PubInv/EcoPot/hypo-Round_vs_Flat/Screenshot 2025-10-10 at 23.31.12.png

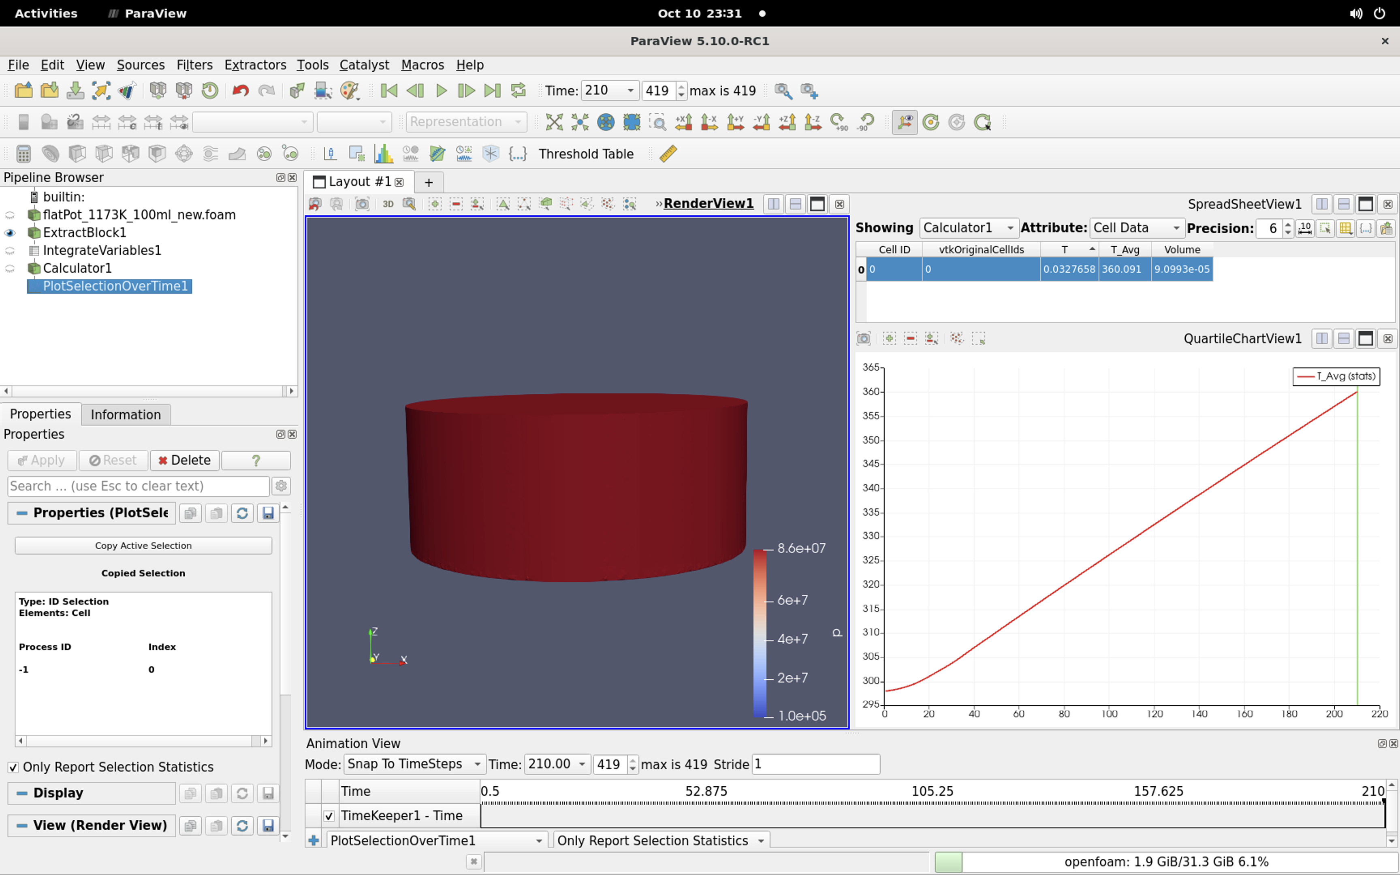
hypo-Round_vs_Flat/Screenshot 2025-10-10 at 23.31.12.png
