PubInv/EcoPot/hypo-Round_vs_Flat/Screenshot 2025-10-10 at 23.35.48.png

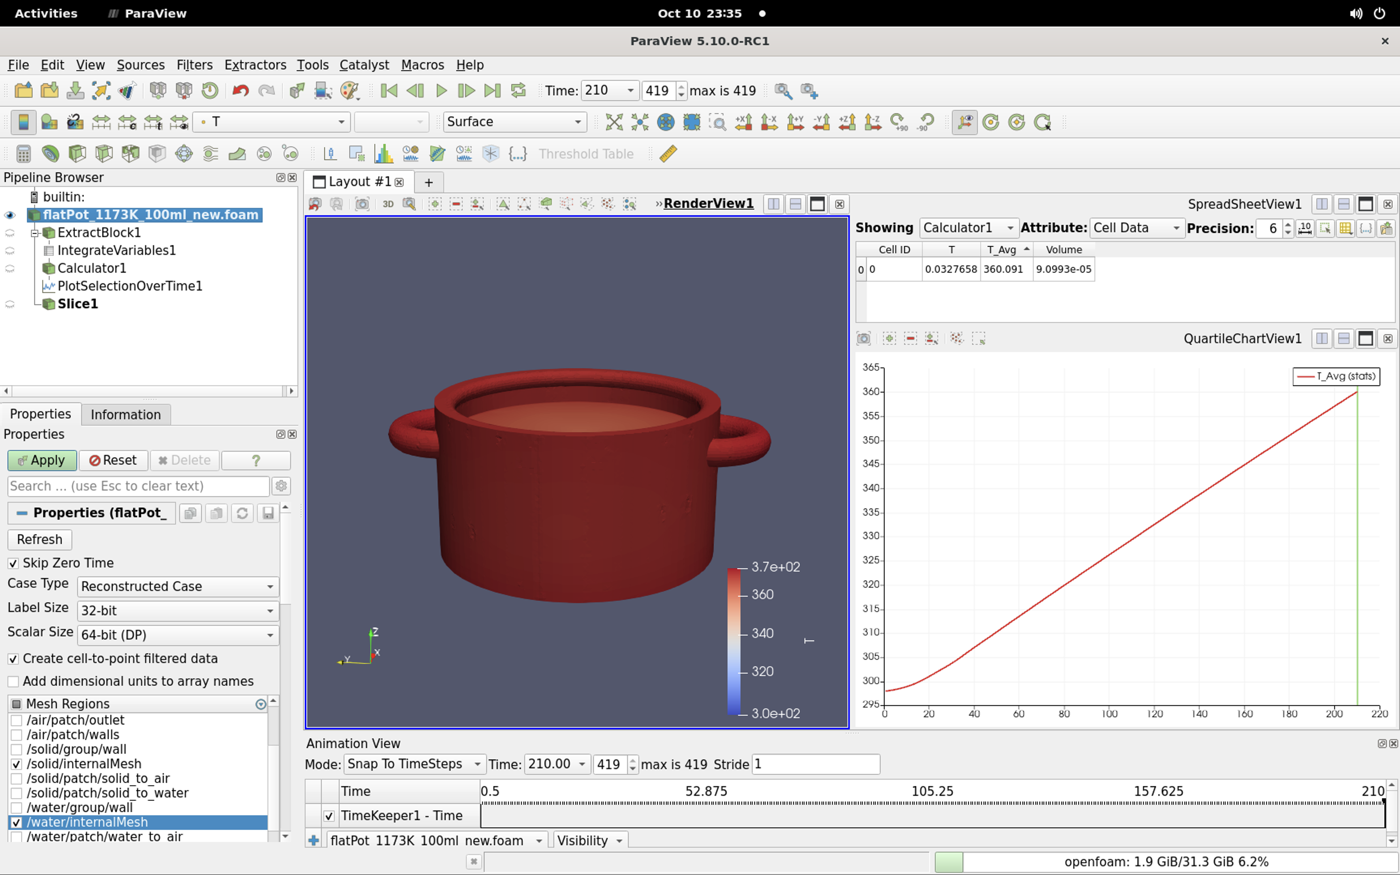
hypo-Round_vs_Flat/Screenshot 2025-10-10 at 23.35.48.png
