PubInv/EcoPot/OpenFOAM/rectangularPot_case/constant/geometry/rectangularPot.stl

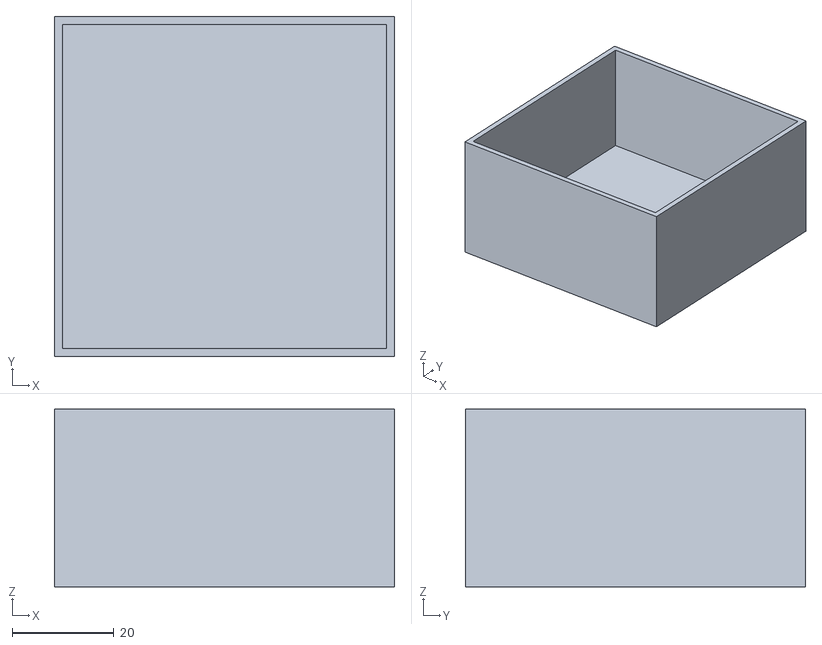
[picture p47: CAD file, 2025-06-29]
OpenFOAM/rectangularPot_case/constant/geometry/rectangularPot.stl
67.0 x 67.0 x 35.1
