PubInv/EcoPot/OpenFOAM/rectangularPot_case/templates/constant/geometry/rectangularPotContent.stl

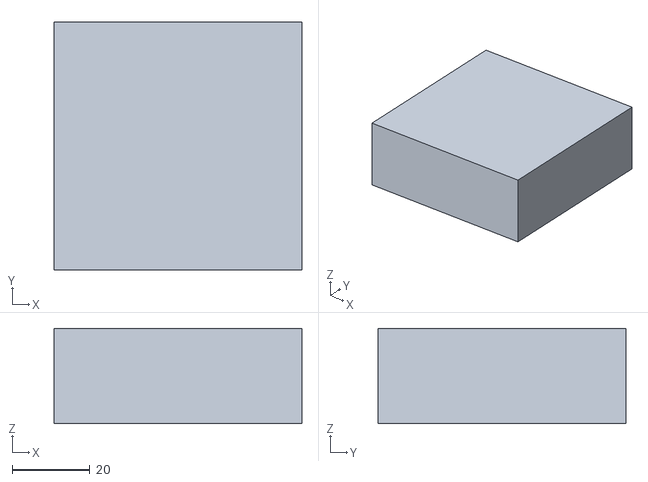
[picture p48: CAD file, 2025-06-29]
OpenFOAM/rectangularPot_case/templates/constant/geometry/rectangularPotContent.stl
63.8 x 63.8 x 24.5
