PubInv/EcoPot/OpenFOAM/roundPot_873K_100ml_36thickFins/constant/geometry/pot_roundfins.stl

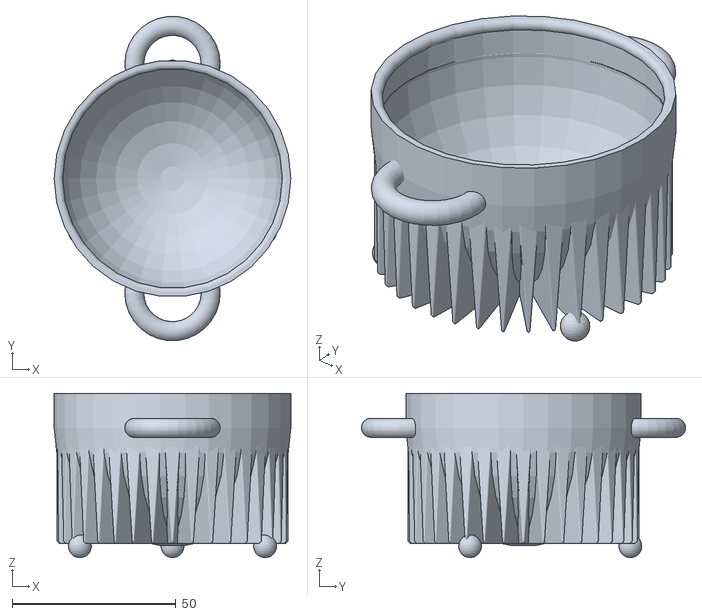
[picture p49: CAD file, 2025-12-26]
OpenFOAM/roundPot_873K_100ml_36thickFins/constant/geometry/pot_roundfins.stl
72.3 x 99.0 x 50.1
