PubInv/EcoPot/OpenFOAM/snappyMultiRegionHeater/constant/triSurface/geom.stl

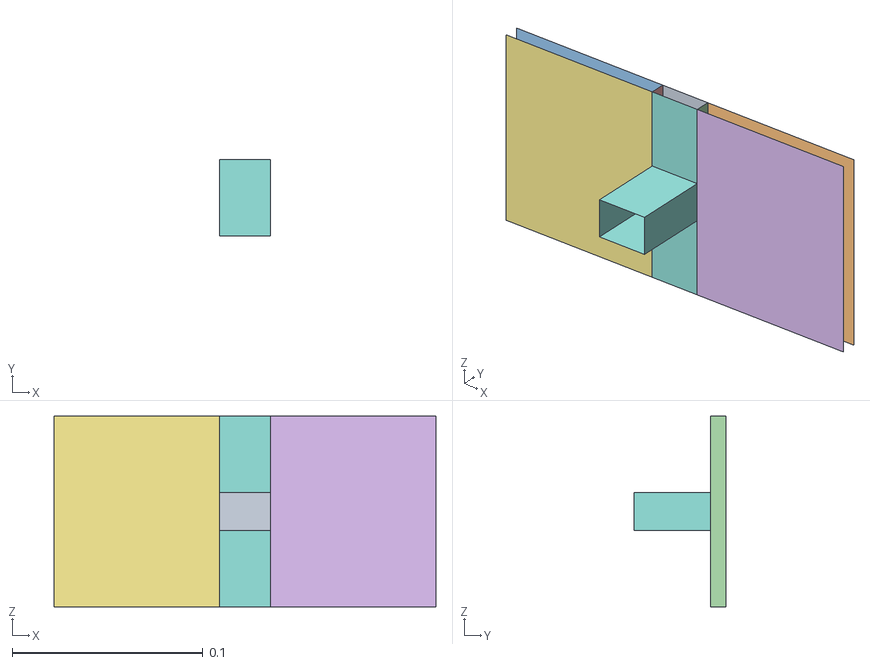
[picture p50: CAD file, 2024-10-04]
OpenFOAM/snappyMultiRegionHeater/constant/triSurface/geom.stl
0.2 x 0.048 x 0.1
topAir_to_heater
leftSolid_to_topAir
rightSolid_to_topAir
leftSolid_to_heater
rightSolid_to_heater
leftSolid_to_bottomAir
rightSolid_to_bottomAir
heater_to_bottomAir
