PubInv/EcoPot/OpenFOAM/wavyPot_873K_100ml_conicalLid/constant/geometry/wavy_water_real.stl

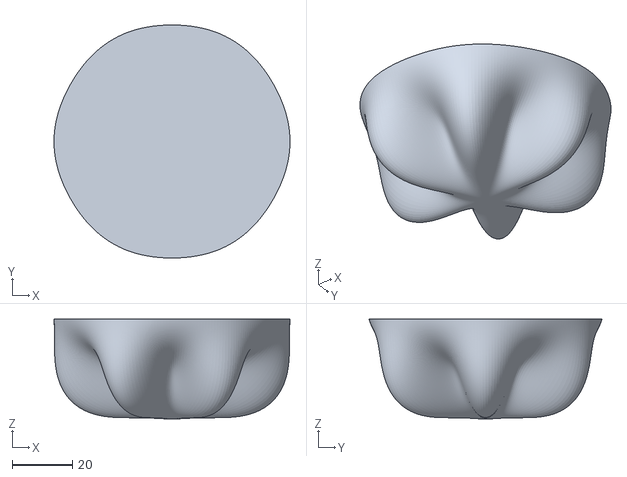
[picture p51: CAD file, 2026-08-23]
OpenFOAM/wavyPot_873K_100ml_conicalLid/constant/geometry/wavy_water_real.stl
78.1 x 77.2 x 33.1
