PubInv/EcoPot/pot-designs/2 Inch Pots used for Shapeways ECOPOT/Standard Pot 2 Inch.SLDPRT

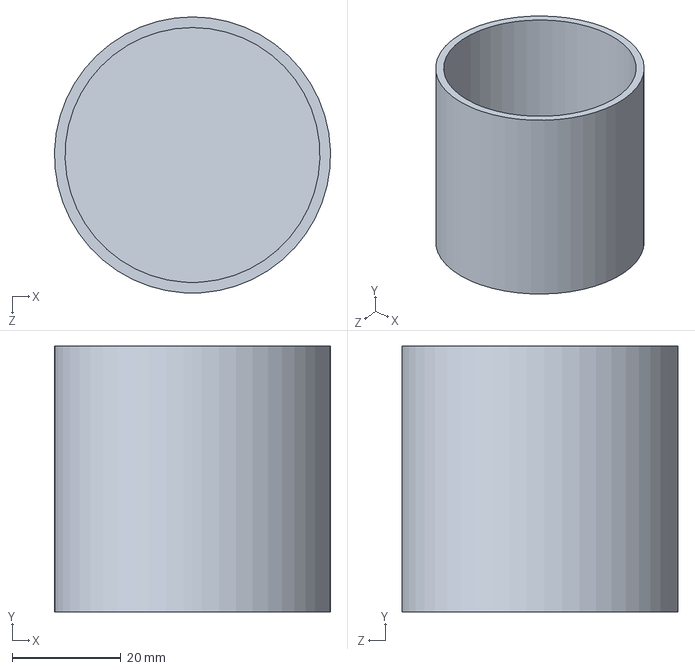
[picture p52: CAD file, 2021-05-05]
pot-designs/2 Inch Pots used for Shapeways ECOPOT/Standard Pot 2 Inch.SLDPRT
50.8 x 48.8 x 50.8 mm
