PubInv/EcoPot/pot-designs/Heat Gun Attachment FreeCAD Sketch.dxf

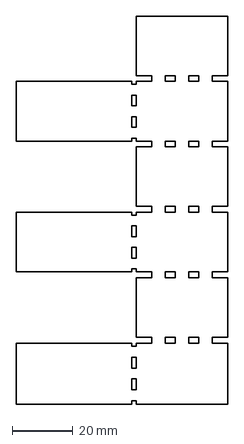
[picture p53: CAD file, 2025-12-03]
pot-designs/Heat Gun Attachment FreeCAD Sketch.dxf
69.5 x 127.7 mm
