PubInv/EcoPot/pot-STLS/TestApparatus.3mf

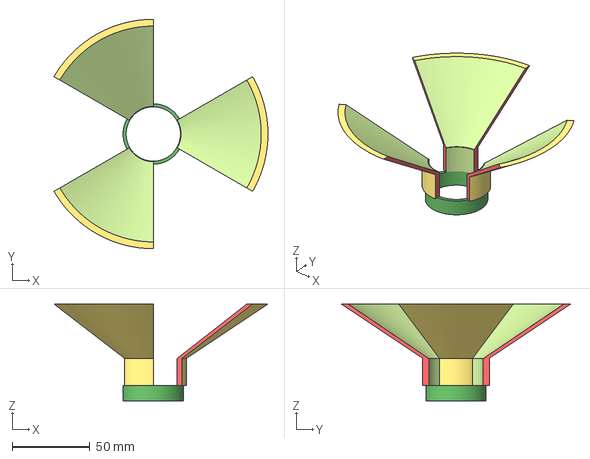
[picture p54: CAD file, 2025-10-04]
pot-STLS/TestApparatus.3mf
138.0 x 147.9 x 62.5 mm
