PubInv/EcoPot/Prototypes and Testing--Rice Team/Models _ Simulations/Generation 1 Models - Concept Ideation and Creation/Helical Vane Inner Pot v2.SLDPRT

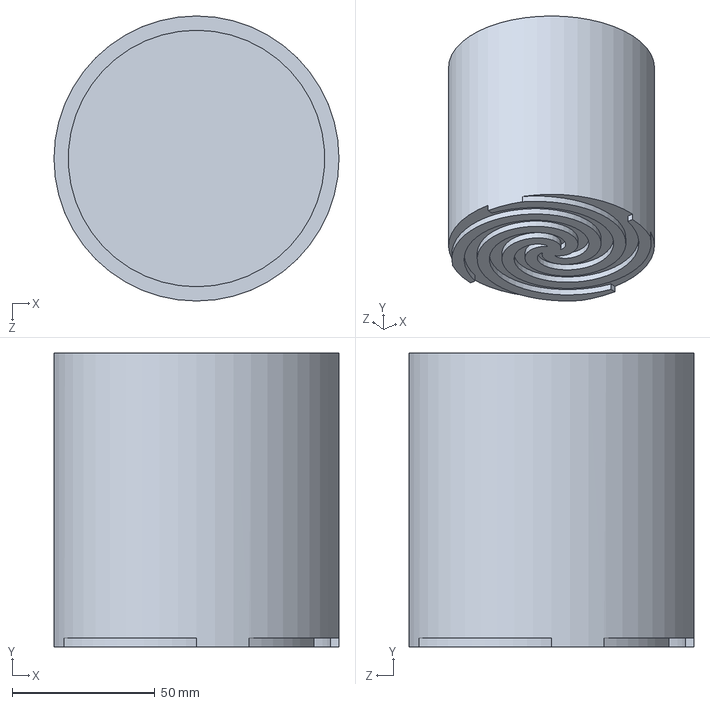
[picture p55: CAD file, 2021-06-08]
Prototypes and Testing--Rice Team/Models _ Simulations/Generation 1 Models - Concept Ideation and Creation/Helical Vane Inner Pot v2.SLDPRT
100.0 x 103.0 x 100.0 mm
