PubInv/EcoPot/Prototypes and Testing--Rice Team/Models _ Simulations/Generation 2 Models - 2 Inch Finned Shapeways Models /Horizontal Finned Pot 2 Inch.SLDPRT

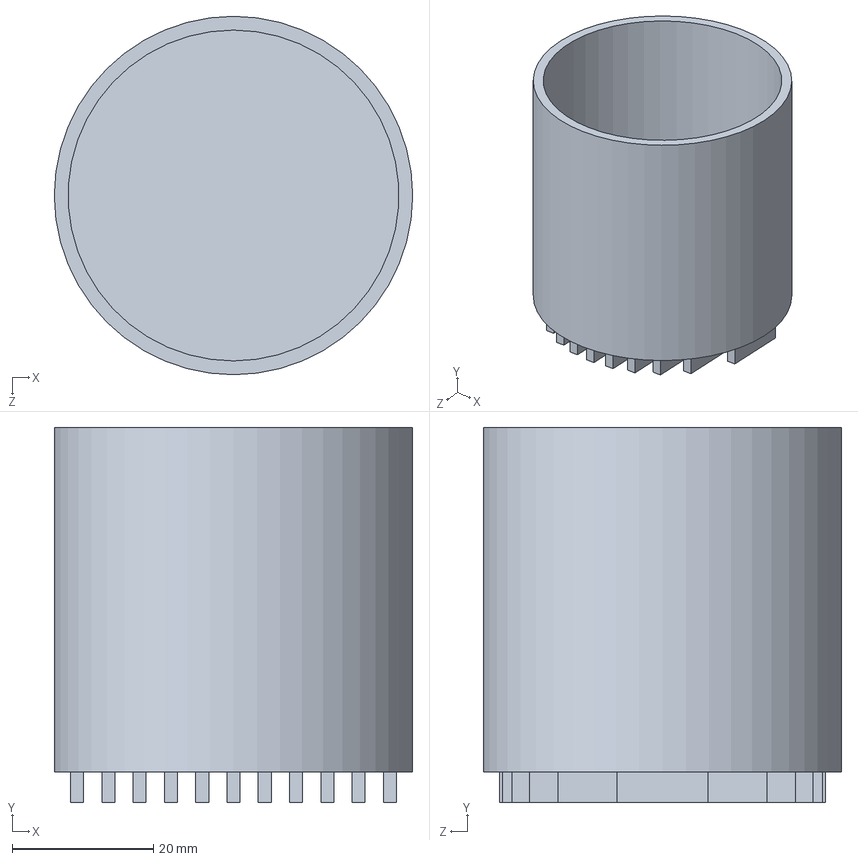
[picture p56: CAD file, 2021-06-08]
Prototypes and Testing--Rice Team/Models _ Simulations/Generation 2 Models - 2 Inch Finned Shapeways Models /Horizontal Finned Pot 2 Inch.SLDPRT
50.8 x 53.2 x 50.8 mm
