PubInv/EcoPot/Prototypes and Testing--Rice Team/Models _ Simulations/Proof of Concept Parts and STL files/Standard Pot.STL

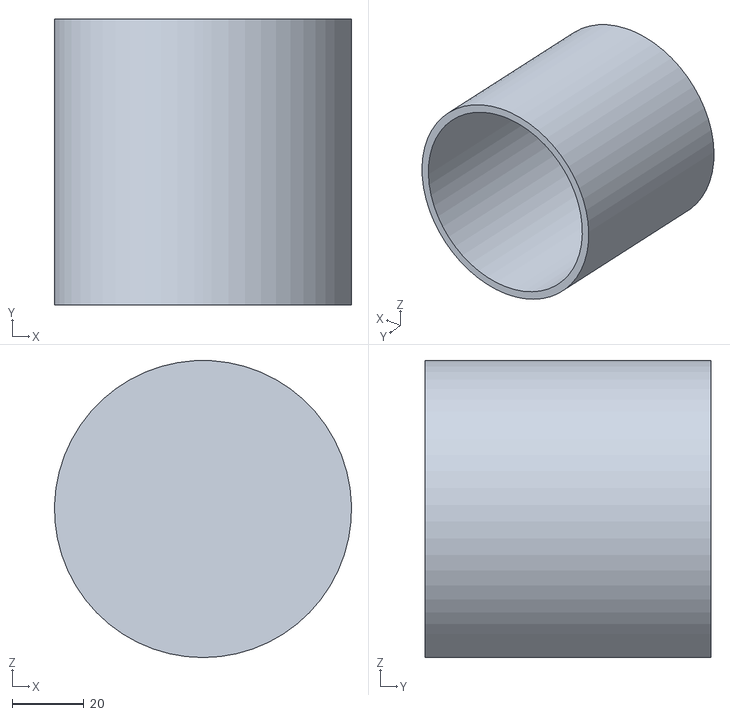
[picture p57: CAD file, 2021-06-08]
Prototypes and Testing--Rice Team/Models _ Simulations/Proof of Concept Parts and STL files/Standard Pot.STL
82.5 x 79.4 x 82.5
