PubInv/EcoPot/Prototypes and Testing--Rice Team/Models _ Simulations/Standard Pot 2 Inch Sim Setup.SLDPRT

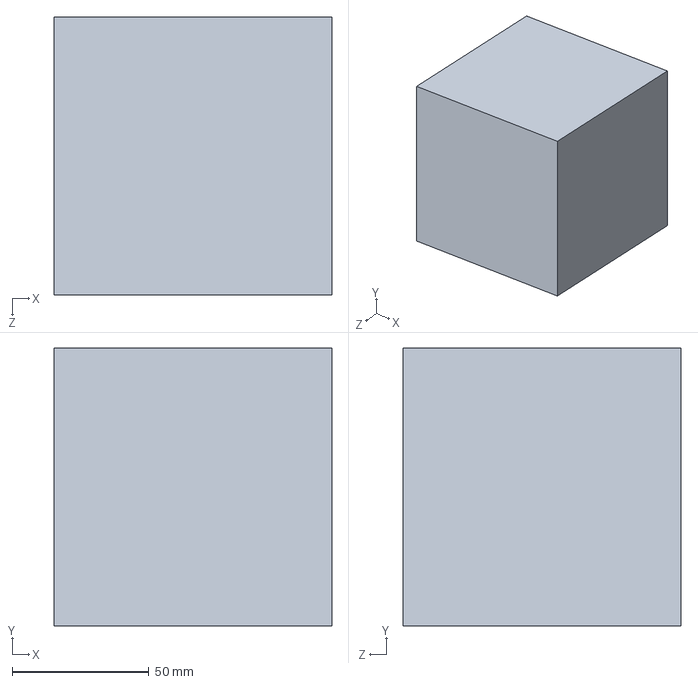
[picture p58: CAD file, 2021-06-08]
Prototypes and Testing--Rice Team/Models _ Simulations/Standard Pot 2 Inch Sim Setup.SLDPRT
101.6 x 101.6 x 101.6 mm
