PubInv/EcoPot/WavyPotSTEP/wavy_pot_vertical_meridians.step

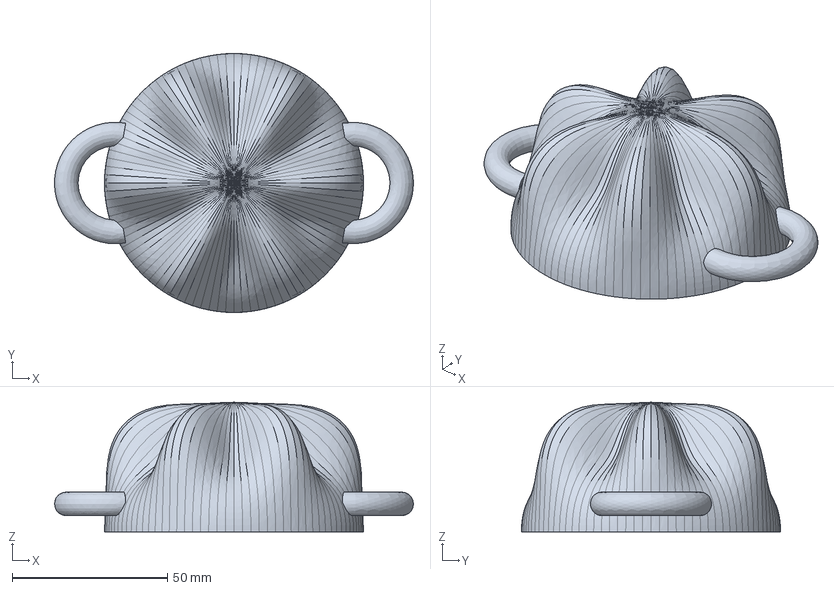
[picture p59: CAD file, 2026-05-20]
WavyPotSTEP/wavy_pot_vertical_meridians.step
115.7 x 83.5 x 41.7 mm
