PubInv/EcoPot/hypo-Round_vs_Flat/Flat_Bottom_Pot.stl

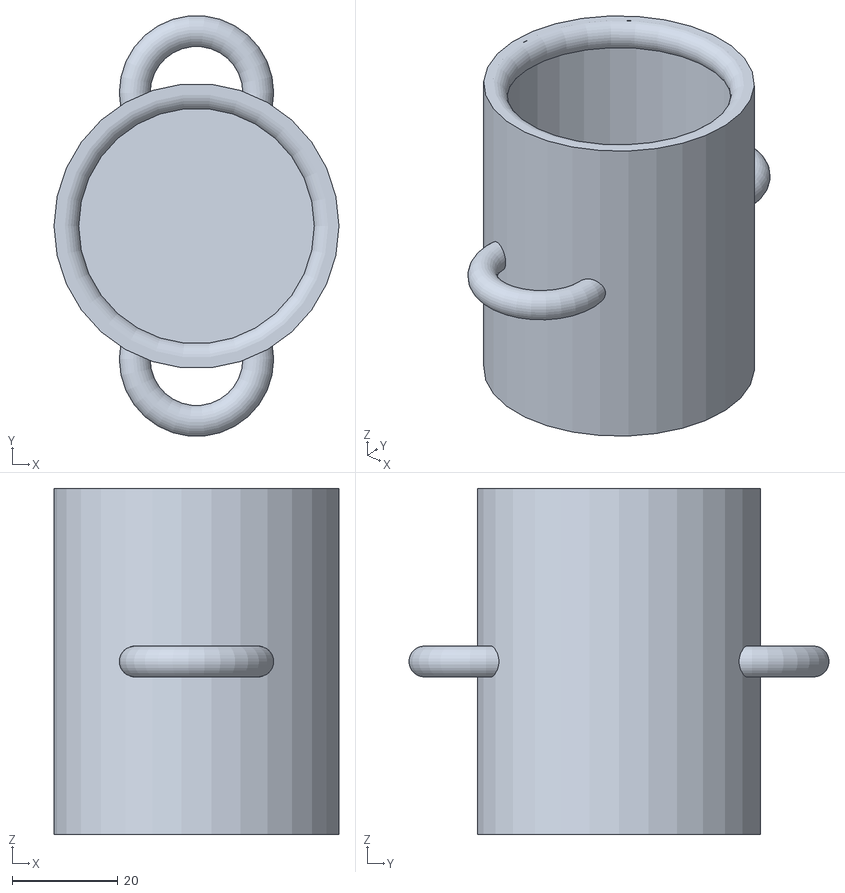
[picture p60: CAD file, 2025-07-09]
hypo-Round_vs_Flat/Flat_Bottom_Pot.stl
53.8 x 79.3 x 65.4
