PubInv/EcoPot/OpenFOAM/erlenmeyer_pot_16605mm_wall_thickness/constant/geometry/flatLid.stl

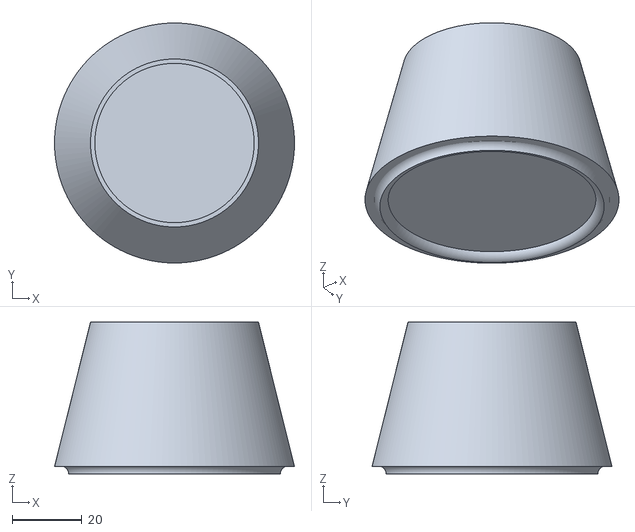
[picture p61: CAD file, 2026-04-26]
OpenFOAM/erlenmeyer_pot_16605mm_wall_thickness/constant/geometry/flatLid.stl
68.7 x 68.7 x 43.4
