PubInv/EcoPot/OpenFOAM/flatPot_1173K_100ml_widePot/constant/geometry/flatPotContentNewOne.stl

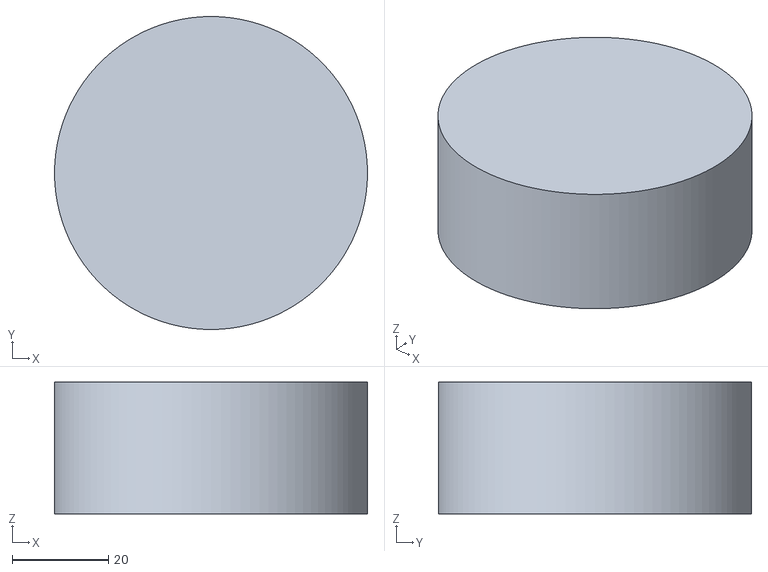
[picture p62: CAD file, 2025-10-10]
OpenFOAM/flatPot_1173K_100ml_widePot/constant/geometry/flatPotContentNewOne.stl
65.1 x 65.1 x 27.4
