PubInv/EcoPot/OpenFOAM/wavyPot_873K_100ml_conicalLid/constant/geometry/conicalLid.stl

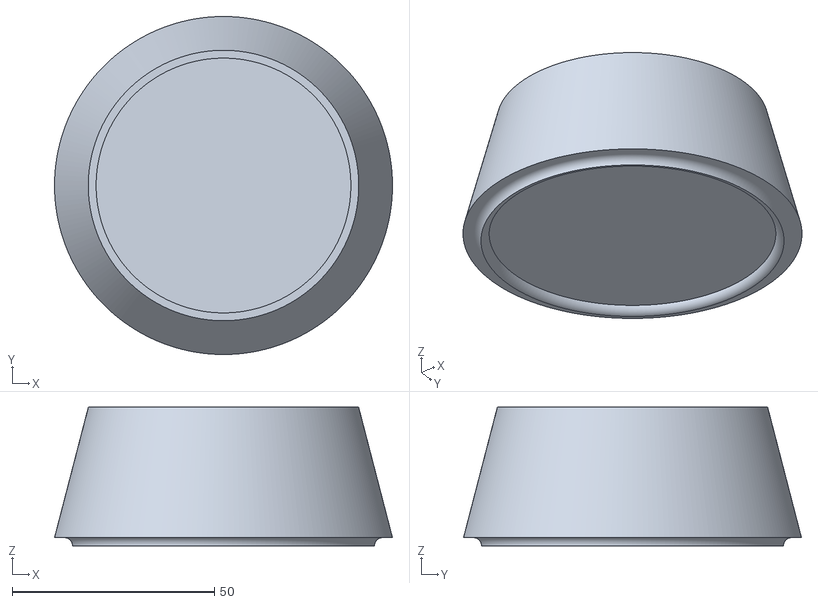
[picture p63: CAD file, 2026-08-23]
OpenFOAM/wavyPot_873K_100ml_conicalLid/constant/geometry/conicalLid.stl
83.5 x 83.5 x 34.2
