PubInv/EcoPot/pot-designs/2 Inch Pots used for Shapeways ECOPOT/Radial Half Finned Pot Rounded 2 Inch.SLDPRT

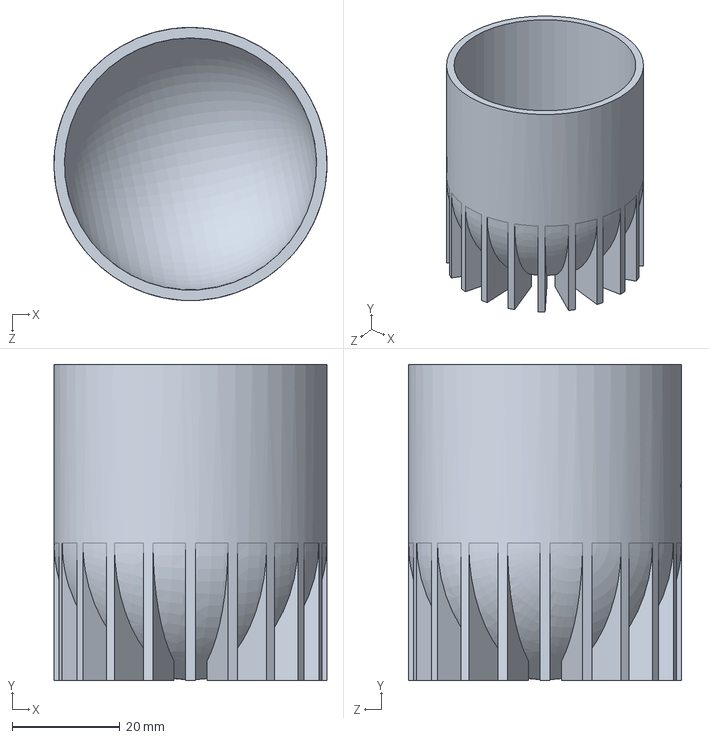
[picture p64: CAD file, 2021-05-05]
pot-designs/2 Inch Pots used for Shapeways ECOPOT/Radial Half Finned Pot Rounded 2 Inch.SLDPRT
50.8 x 58.8 x 50.8 mm
