PubInv/EcoPot/pot-designs/Heat Gun Attachment FreeCAD v1.dxf

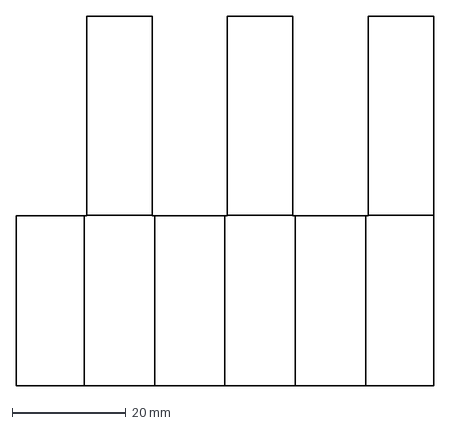
[picture p65: CAD file, 2025-11-05]
pot-designs/Heat Gun Attachment FreeCAD v1.dxf
73.5 x 65.1 mm
