PubInv/EcoPot/pot-STLS/ParameterizedPotDesigns_pot.stl

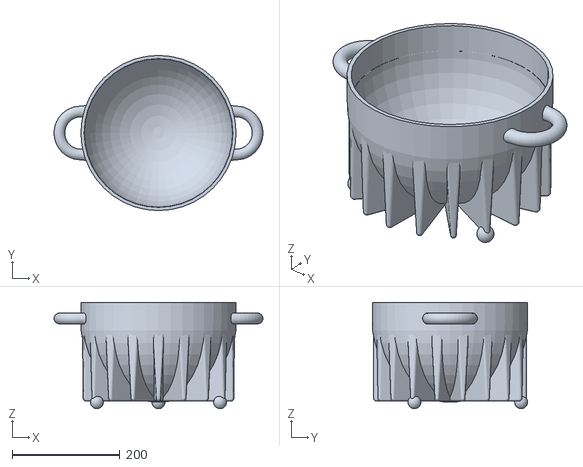
[picture p66: CAD file, 2025-02-19]
pot-STLS/ParameterizedPotDesigns_pot.stl
388.2 x 288.2 x 197.5
