PubInv/EcoPot/Prototypes and Testing--Rice Team/Models _ Simulations/Generation 1 Models - Concept Ideation and Creation/Ecopot - basic pot.SLDPRT

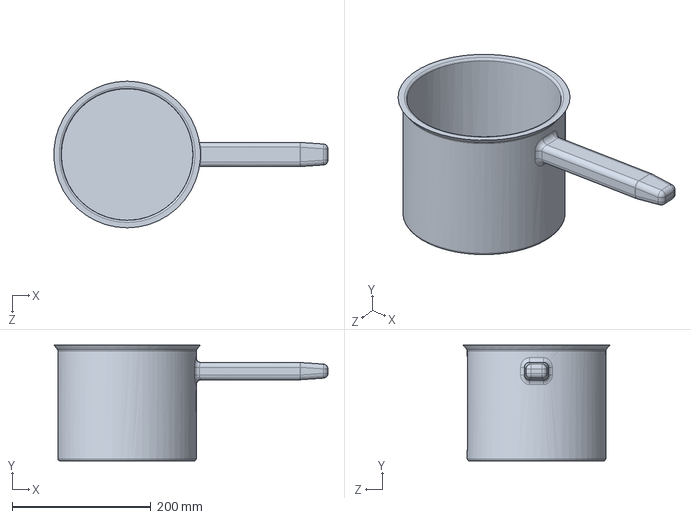
[picture p67: CAD file, 2021-06-08]
Prototypes and Testing--Rice Team/Models _ Simulations/Generation 1 Models - Concept Ideation and Creation/Ecopot - basic pot.SLDPRT
395.6 x 167.0 x 211.7 mm
