PubInv/EcoPot/Prototypes and Testing--Rice Team/Models _ Simulations/Generation 3 Models - Half Radial Fin Iterations + Fin Guard Models/Radial Half Finned Pot_40 Fins.SLDPRT

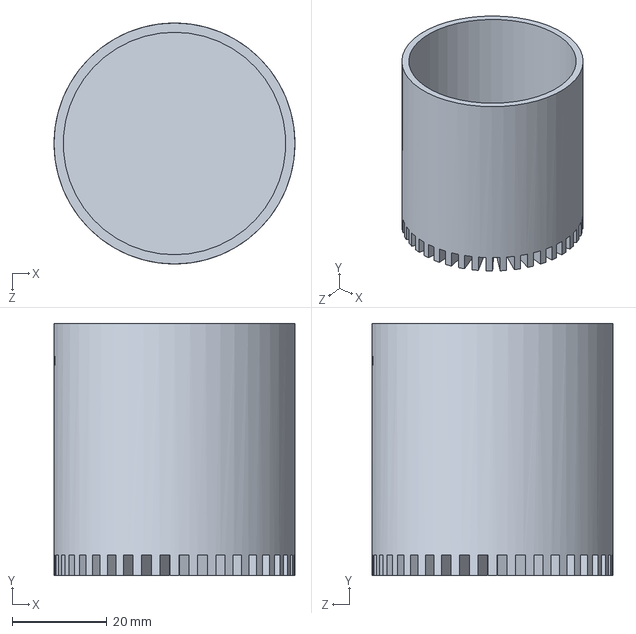
[picture p68: CAD file, 2021-06-08]
Prototypes and Testing--Rice Team/Models _ Simulations/Generation 3 Models - Half Radial Fin Iterations + Fin Guard Models/Radial Half Finned Pot_40 Fins.SLDPRT
50.8 x 53.2 x 50.8 mm
