PubInv/EcoPot/Prototypes and Testing--Rice Team/Models _ Simulations/Proof of Concept Parts and STL files/Helical Vane Outer Pot.STL

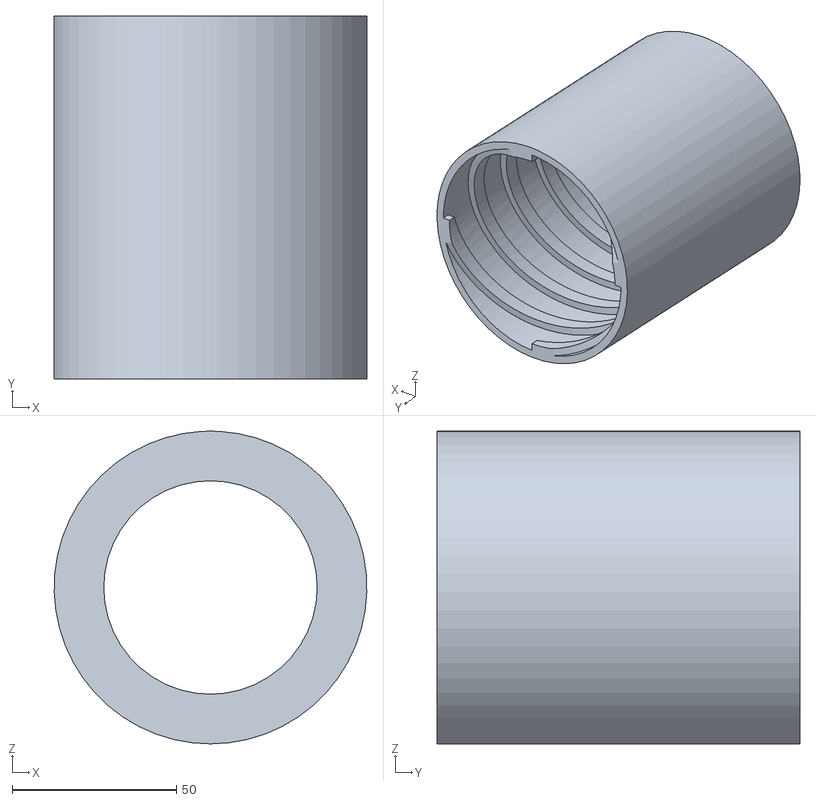
[picture p69: CAD file, 2021-06-08]
Prototypes and Testing--Rice Team/Models _ Simulations/Proof of Concept Parts and STL files/Helical Vane Outer Pot.STL
95.2 x 110.6 x 95.2
