PubInv/EcoPot/hypo-Round_vs_Flat/Rounded_Bottom_Pot.stl

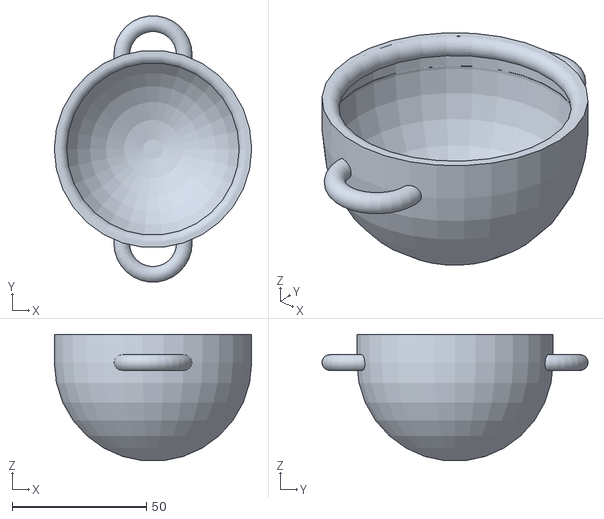
[picture p70: CAD file, 2025-07-09]
hypo-Round_vs_Flat/Rounded_Bottom_Pot.stl
73.5 x 99.0 x 47.0
