PubInv/EcoPot/OpenFOAM/erlenmeyer_pot_16605mm_wall_thickness/constant/geometry/erlenmeyerPotContent.stl

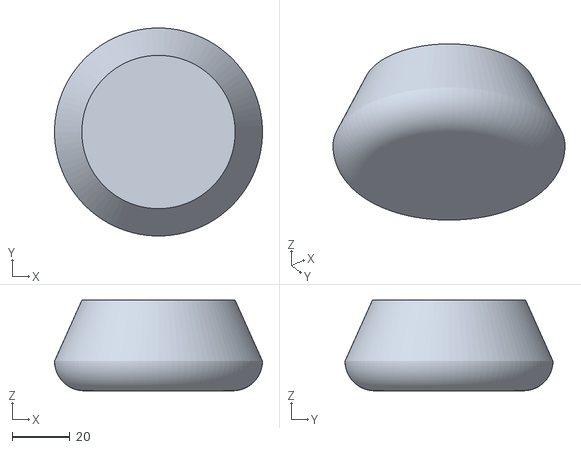
[picture p71: CAD file, 2026-04-26]
OpenFOAM/erlenmeyer_pot_16605mm_wall_thickness/constant/geometry/erlenmeyerPotContent.stl
72.0 x 72.0 x 31.4
