PubInv/EcoPot/OpenFOAM/flatPot_1173K_100ml_widePot/constant/geometry/flatPotContentNew.stl

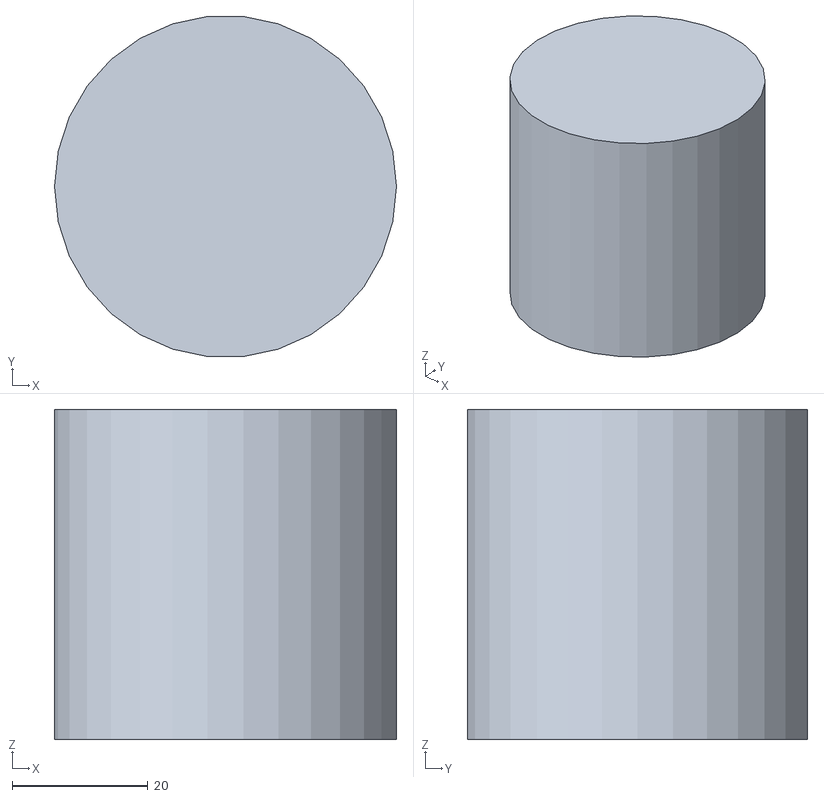
[picture p72: CAD file, 2025-07-09]
OpenFOAM/flatPot_1173K_100ml_widePot/constant/geometry/flatPotContentNew.stl
50.3 x 50.0 x 48.6
