PubInv/EcoPot/pot-designs/2 Inch Pots used for Shapeways ECOPOT/Radial Pot Rounded 2 Inch.SLDPRT

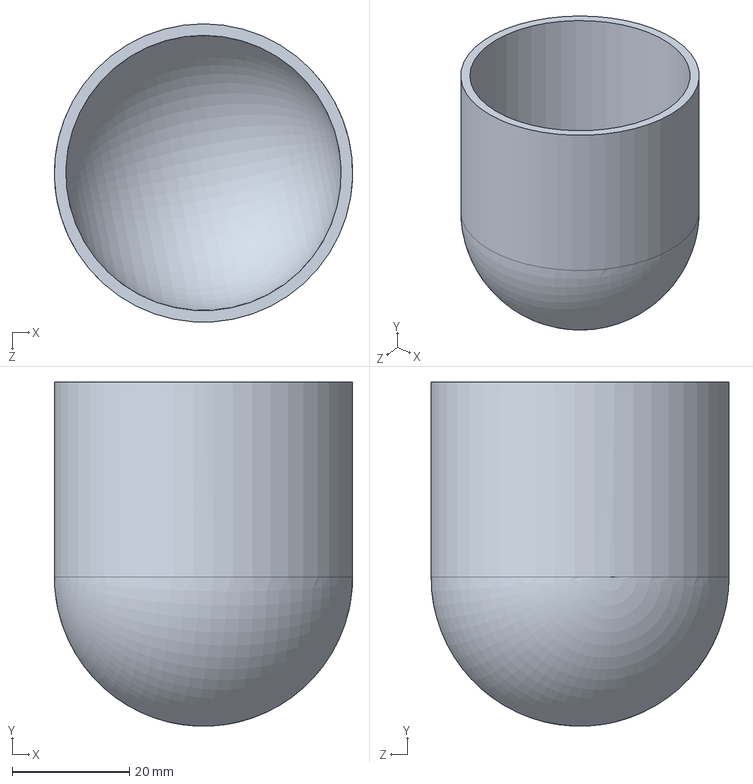
[picture p73: CAD file, 2021-05-05]
pot-designs/2 Inch Pots used for Shapeways ECOPOT/Radial Pot Rounded 2 Inch.SLDPRT
50.8 x 58.6 x 50.8 mm
