PubInv/EcoPot/pot-STLS/Crucible.stl

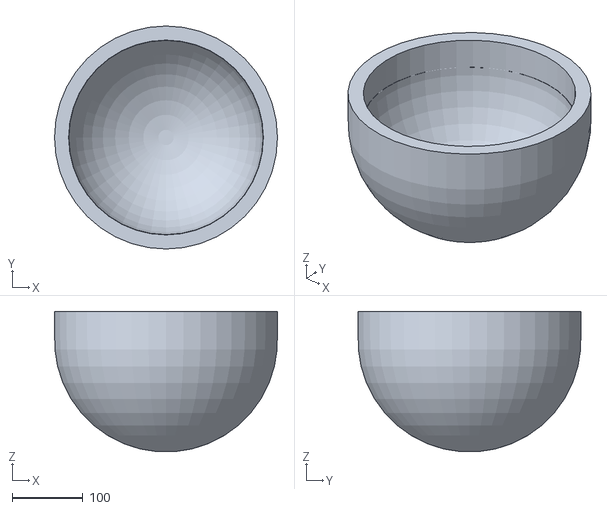
[picture p74: CAD file, 2024-09-18]
pot-STLS/Crucible.stl
316.2 x 316.2 x 199.1
