PubInv/EcoPot/Prototypes and Testing--Rice Team/Models _ Simulations/Generation 1 Models - Concept Ideation and Creation/Helical Vane Outer Pot.SLDPRT

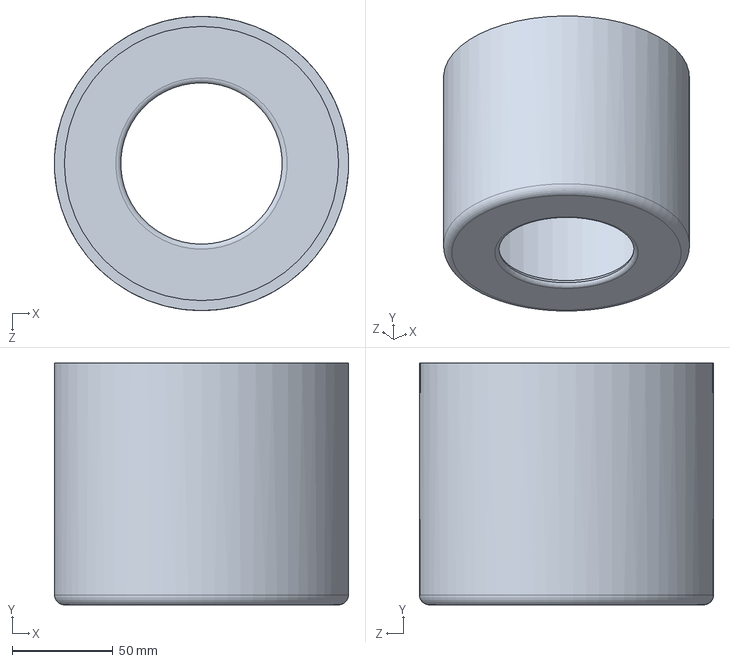
[picture p75: CAD file, 2021-06-08]
Prototypes and Testing--Rice Team/Models _ Simulations/Generation 1 Models - Concept Ideation and Creation/Helical Vane Outer Pot.SLDPRT
145.9 x 120.0 x 146.0 mm
