PubInv/EcoPot/Prototypes and Testing--Rice Team/Models _ Simulations/Generation 2 Models - 2 Inch Finned Shapeways Models /Horizontal Finned Pot.SLDPRT

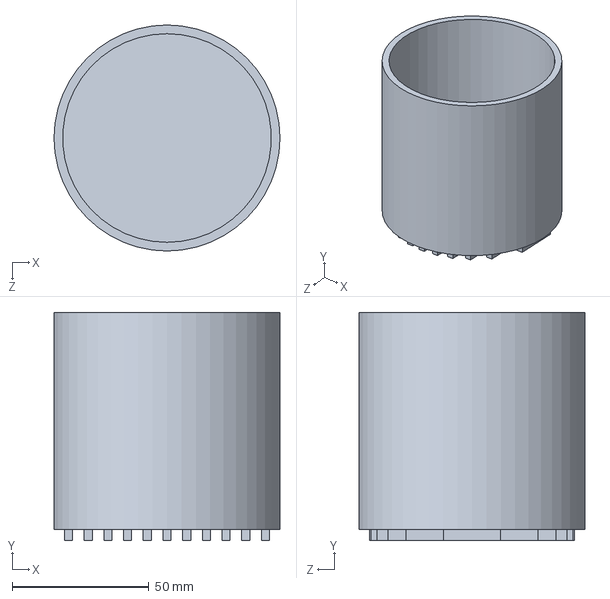
[picture p76: CAD file, 2021-06-08]
Prototypes and Testing--Rice Team/Models _ Simulations/Generation 2 Models - 2 Inch Finned Shapeways Models /Horizontal Finned Pot.SLDPRT
82.5 x 83.4 x 82.5 mm
