PubInv/EcoPot/Prototypes and Testing--Rice Team/Models _ Simulations/Proof of Concept Parts and STL files/Helical Vane Inner Pot.SLDPRT

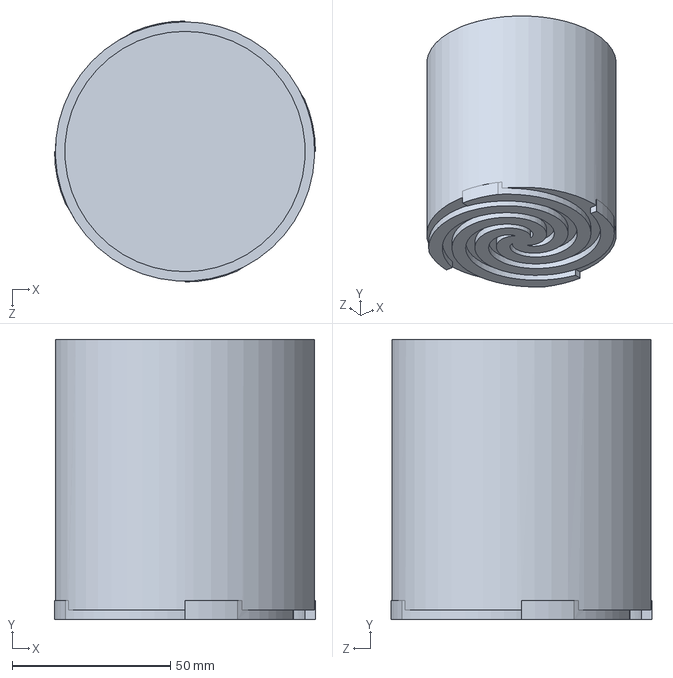
[picture p77: CAD file, 2021-06-08]
Prototypes and Testing--Rice Team/Models _ Simulations/Proof of Concept Parts and STL files/Helical Vane Inner Pot.SLDPRT
82.5 x 88.5 x 82.5 mm
