PubInv/EcoPot/OpenFOAM/erlenmeyer_pot_16605mm_wall_thickness/constant/geometry/flatPot.stl

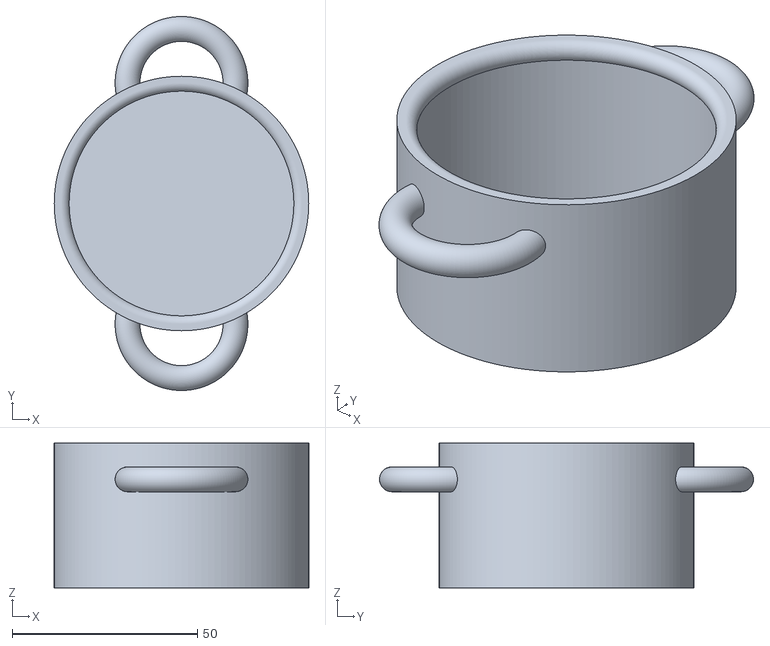
[picture p78: CAD file, 2026-04-26]
OpenFOAM/erlenmeyer_pot_16605mm_wall_thickness/constant/geometry/flatPot.stl
68.7 x 100.9 x 39.1
