PubInv/EcoPot/OpenFOAM/wavyPot_873K_100ml_conicalLid/constant/geometry/air_fire.stl

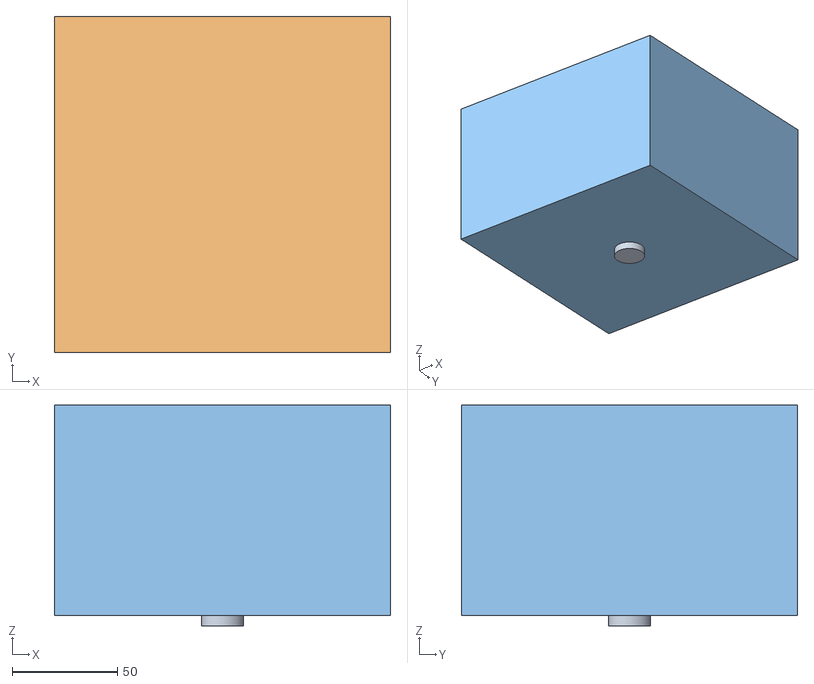
[picture p79: CAD file, 2026-08-23]
OpenFOAM/wavyPot_873K_100ml_conicalLid/constant/geometry/air_fire.stl
160.0 x 160.0 x 105.0
inlet
outlet
walls
