PubInv/EcoPot/Prototypes and Testing--Rice Team/Models _ Simulations/Generation 1 Models - Concept Ideation and Creation/Adjustable Pot Skirt.SLDPRT

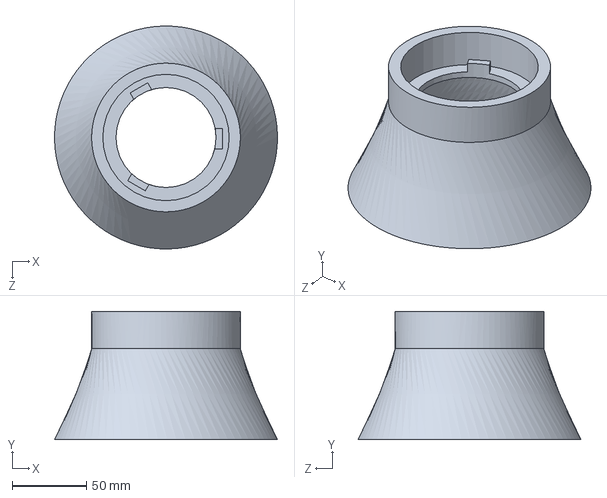
[picture p80: CAD file, 2021-06-08]
Prototypes and Testing--Rice Team/Models _ Simulations/Generation 1 Models - Concept Ideation and Creation/Adjustable Pot Skirt.SLDPRT
150.0 x 86.4 x 150.0 mm
