PubInv/EcoPot/Prototypes and Testing--Rice Team/Models _ Simulations/Generation 3 Models - Half Radial Fin Iterations + Fin Guard Models/Fin Guard Wireframe.SLDPRT

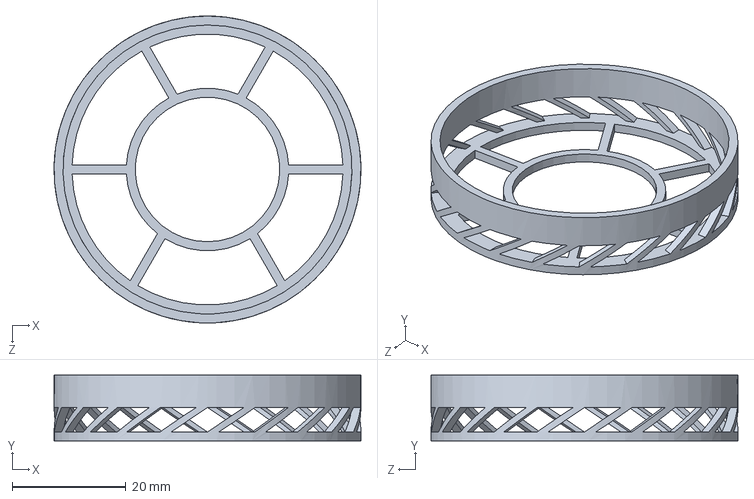
[picture p81: CAD file, 2021-06-08]
Prototypes and Testing--Rice Team/Models _ Simulations/Generation 3 Models - Half Radial Fin Iterations + Fin Guard Models/Fin Guard Wireframe.SLDPRT
54.0 x 11.6 x 54.0 mm
