PubInv/EcoPot/OpenFOAM/erlenmeyer_pot_16605mm_wall_thickness/constant/geometry/air.stl

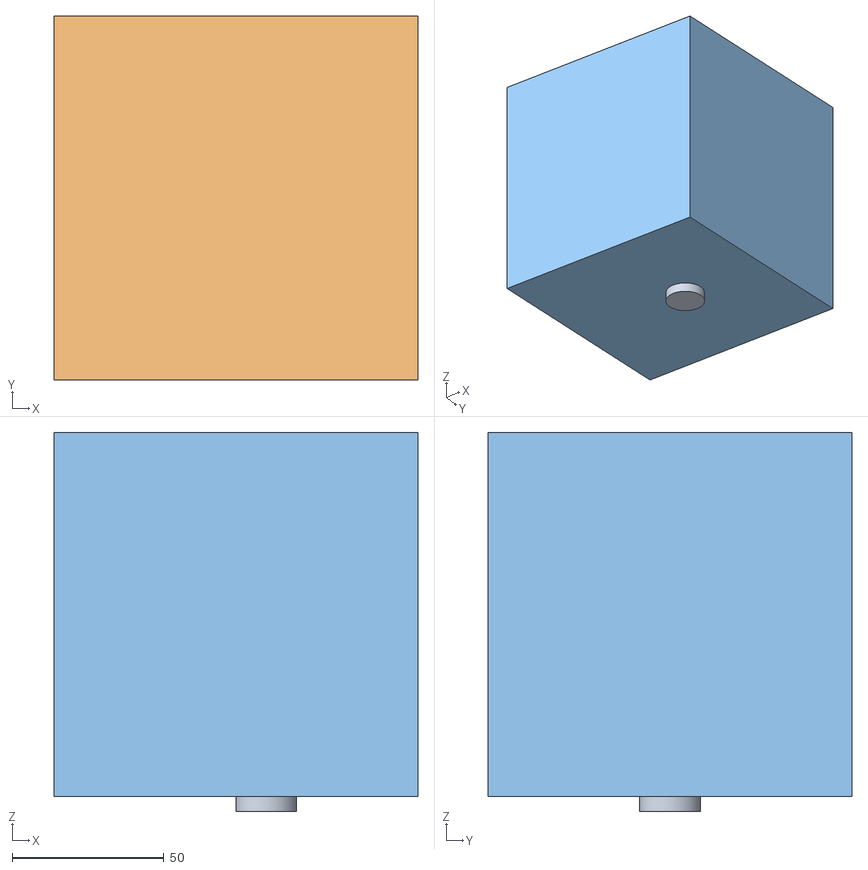
[picture p82: CAD file, 2026-04-26]
OpenFOAM/erlenmeyer_pot_16605mm_wall_thickness/constant/geometry/air.stl
120.0 x 120.0 x 125.0
inlet
outlet
walls
