PubInv/EcoPot/OpenFOAM/flatPot_1173K_100ml_widePot/constant/geometry/flatPot_mm.stl

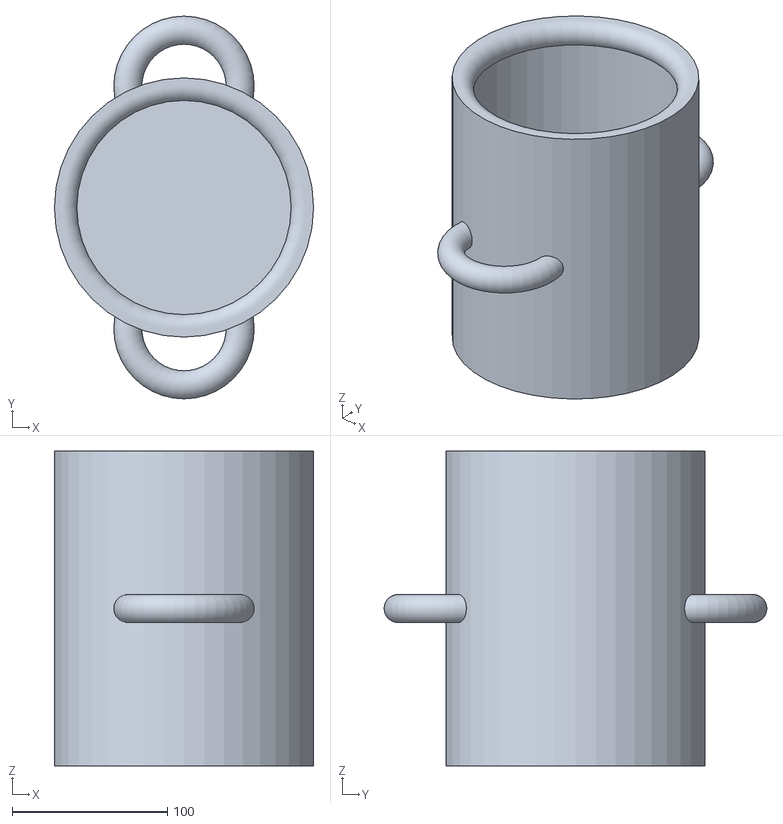
[picture p83: CAD file, 2025-06-07]
OpenFOAM/flatPot_1173K_100ml_widePot/constant/geometry/flatPot_mm.stl
167.2 x 246.9 x 203.2
