PubInv/EcoPot/OpenFOAM/wavyPot_873K_100ml_conicalLid/constant/geometry/headspace.stl

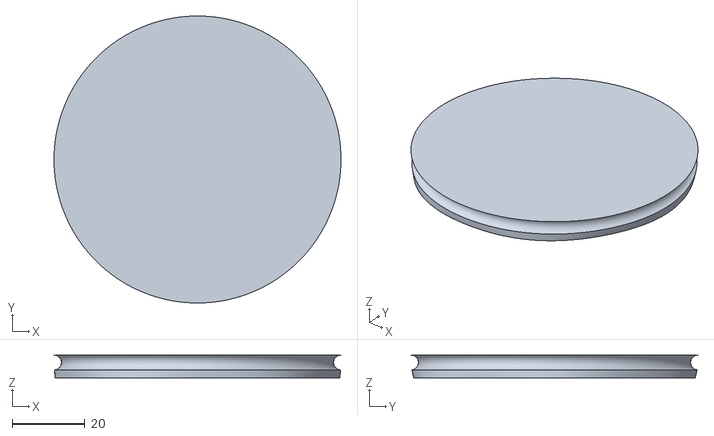
[picture p84: CAD file, 2026-08-23]
OpenFOAM/wavyPot_873K_100ml_conicalLid/constant/geometry/headspace.stl
78.7 x 78.7 x 6.23
