PubInv/EcoPot/OpenFOAM/erlenmeyer_pot_16605mm_wall_thickness/constant/geometry/erlenmeyerPot.stl

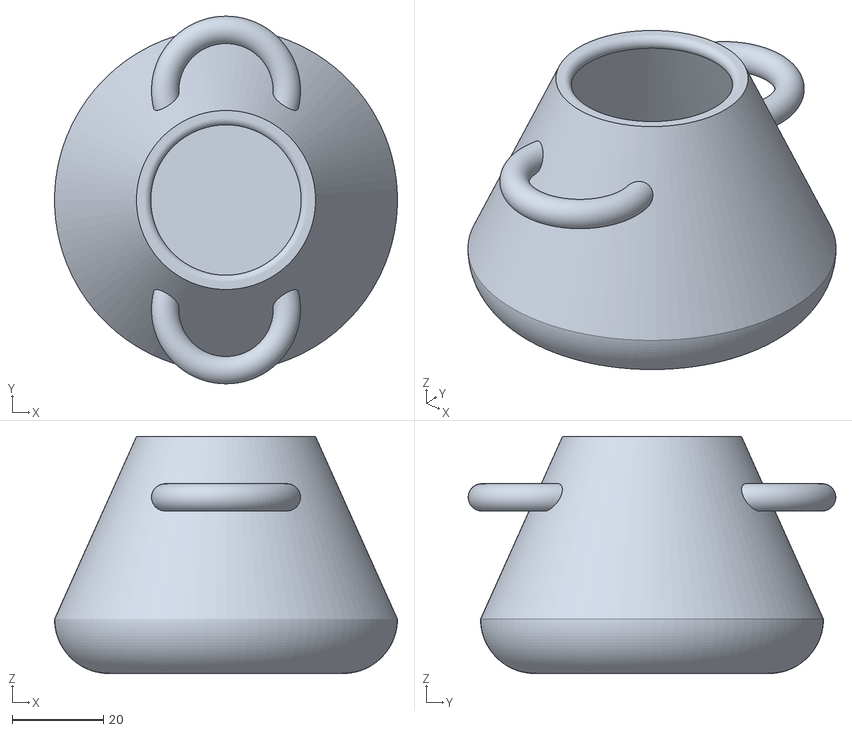
[picture p85: CAD file, 2026-04-26]
OpenFOAM/erlenmeyer_pot_16605mm_wall_thickness/constant/geometry/erlenmeyerPot.stl
75.3 x 80.7 x 52.1
