PubInv/EcoPot/OpenFOAM/wavyPot_873K_100ml_conicalLid/constant/geometry/pot200.stl

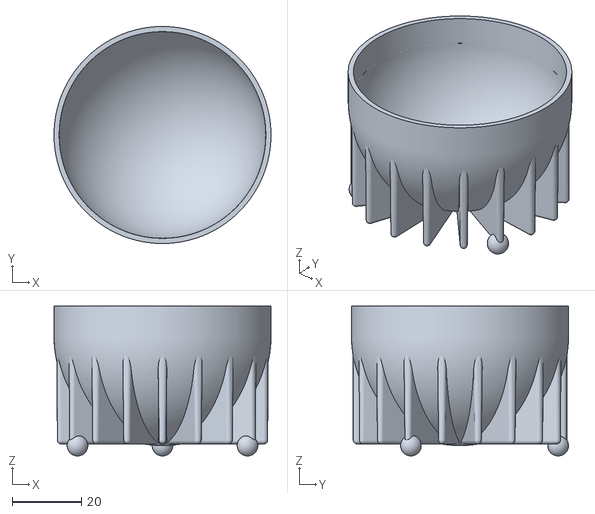
[picture p86: CAD file, 2026-04-26]
OpenFOAM/wavyPot_873K_100ml_conicalLid/constant/geometry/pot200.stl
62.5 x 62.5 x 43.1
