PubInv/EcoPot/Prototypes and Testing--Rice Team/Models _ Simulations/Generation 1 Models - Concept Ideation and Creation/FINNED HEATING PLATE.SLDPRT

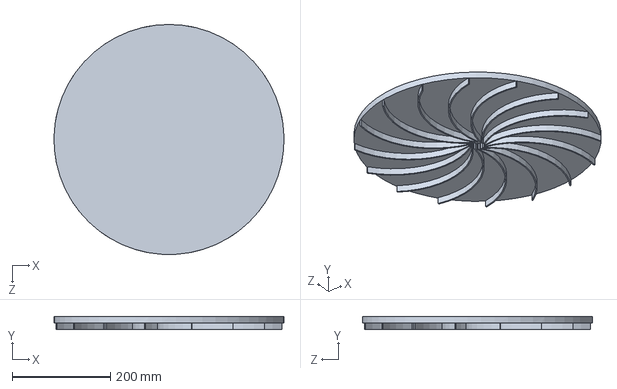
[picture p87: CAD file, 2021-06-08]
Prototypes and Testing--Rice Team/Models _ Simulations/Generation 1 Models - Concept Ideation and Creation/FINNED HEATING PLATE.SLDPRT
467.2 x 25.4 x 467.4 mm
