PubInv/EcoPot/Prototypes and Testing--Rice Team/Models _ Simulations/Generation 3 Models - Half Radial Fin Iterations + Fin Guard Models/Pot with Lid .stl

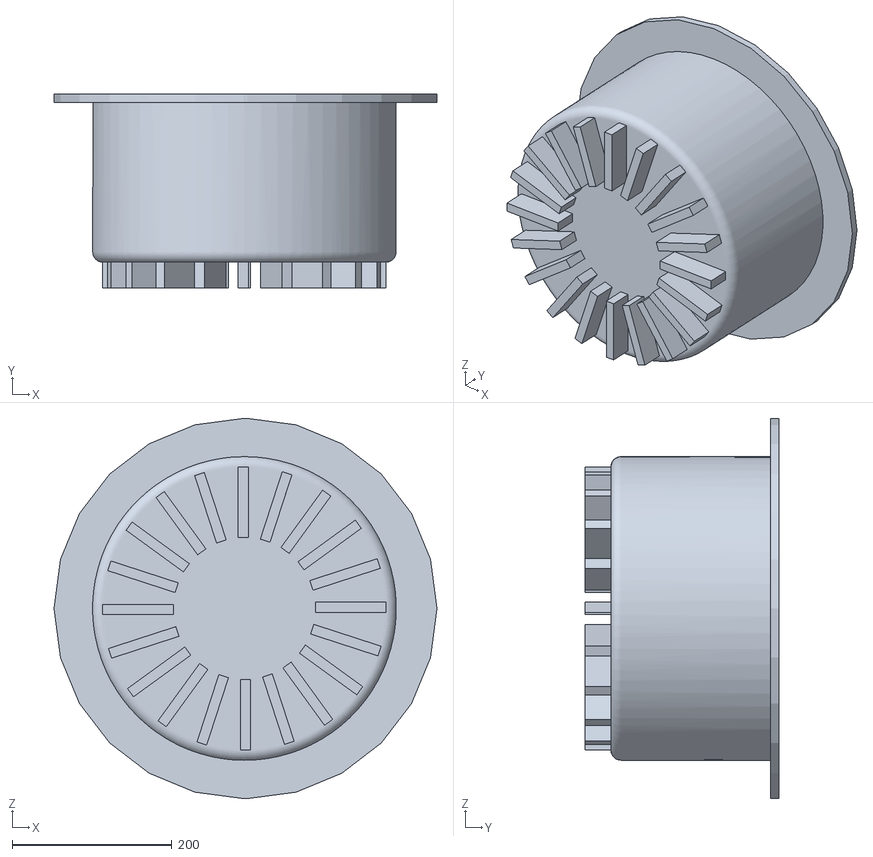
[picture p88: CAD file, 2021-06-08]
Prototypes and Testing--Rice Team/Models _ Simulations/Generation 3 Models - Half Radial Fin Iterations + Fin Guard Models/Pot with Lid .stl
479.3 x 242.6 x 475.9
