PubInv/EcoPot/OpenFOAM/erlenmeyer_pot_16605mm_wall_thickness/constant/geometry/flatPotContent.stl

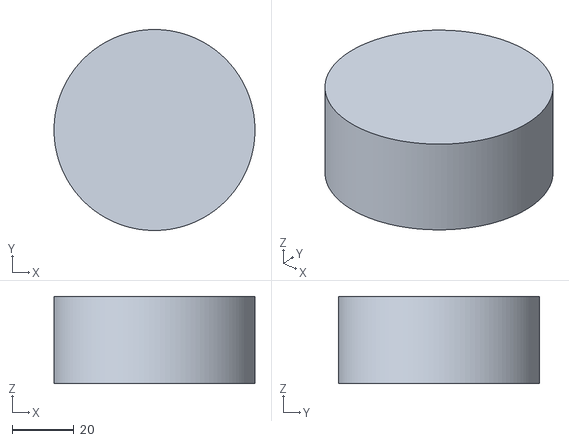
[picture p89: CAD file, 2026-03-23]
OpenFOAM/erlenmeyer_pot_16605mm_wall_thickness/constant/geometry/flatPotContent.stl
65.1 x 65.1 x 28.3
