PubInv/EcoPot/OpenFOAM/wavyPot_873K_100ml_conicalLid/constant/geometry/pot_roundfins.stl

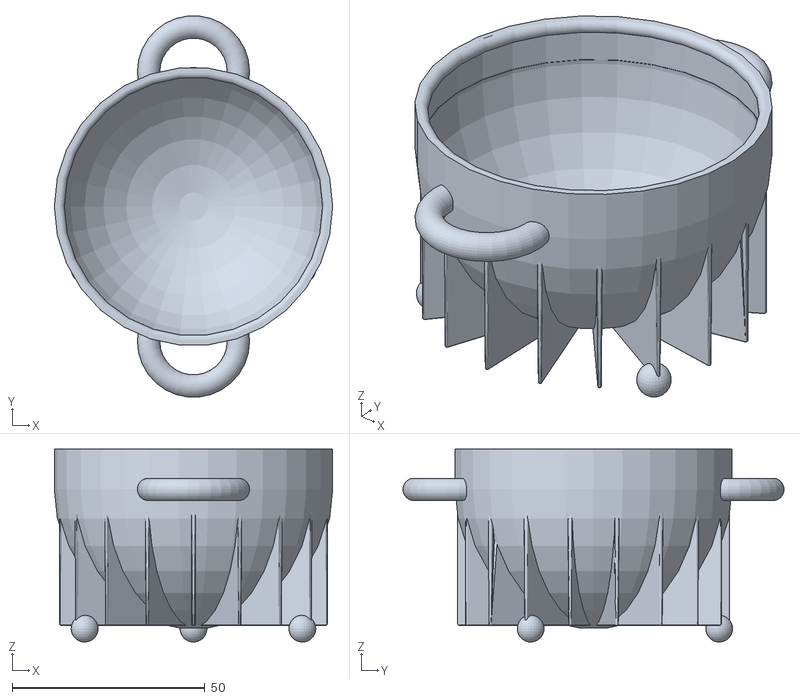
[picture p90: CAD file, 2026-04-26]
OpenFOAM/wavyPot_873K_100ml_conicalLid/constant/geometry/pot_roundfins.stl
72.3 x 99.0 x 50.1
