PubInv/EcoPot/Prototypes and Testing--Rice Team/Models _ Simulations/Generation 1 Models - Concept Ideation and Creation/Helical Vane Outer Pot v3.SLDPRT

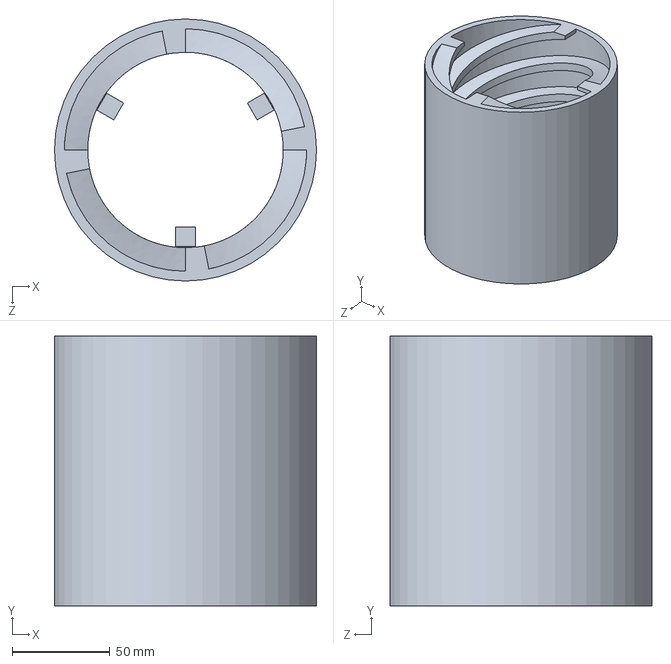
[picture p91: CAD file, 2021-06-08]
Prototypes and Testing--Rice Team/Models _ Simulations/Generation 1 Models - Concept Ideation and Creation/Helical Vane Outer Pot v3.SLDPRT
134.0 x 138.0 x 134.0 mm
