PubInv/EcoPot/OpenFOAM/erlenmeyer_pot_16605mm_wall_thickness/constant/geometry/pot_round.stl

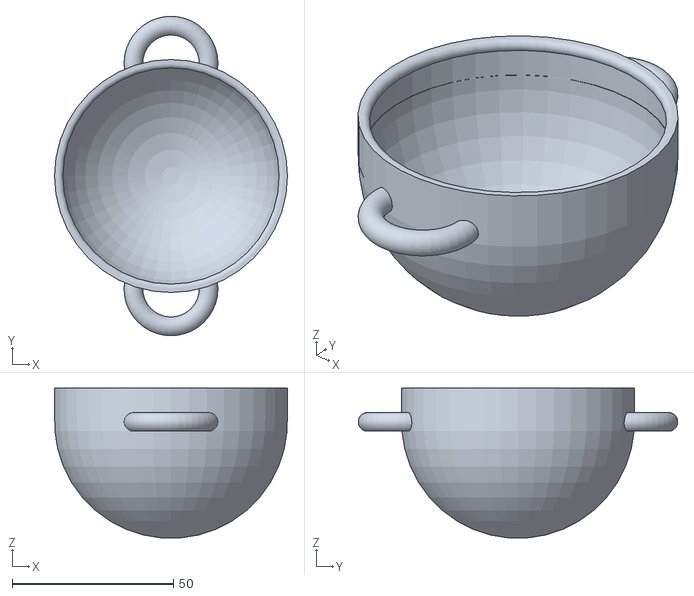
[picture p93: CAD file, 2026-03-23]
OpenFOAM/erlenmeyer_pot_16605mm_wall_thickness/constant/geometry/pot_round.stl
72.3 x 99.1 x 46.5
