PubInv/EcoPot/OpenFOAM/wavyPot_873K_100ml_conicalLid/constant/geometry/ecoPotContentNew.stl

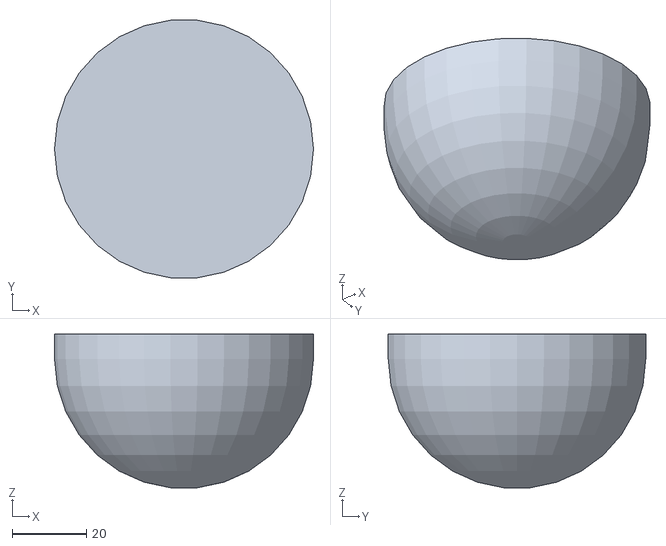
[picture p94: CAD file, 2025-12-26]
OpenFOAM/wavyPot_873K_100ml_conicalLid/constant/geometry/ecoPotContentNew.stl
70.0 x 69.6 x 41.5
