PubInv/EcoPot/Prototypes and Testing--Rice Team/Models _ Simulations/Generation 3 Models - Half Radial Fin Iterations + Fin Guard Models/Life Sized Half Radial Pot_Scaled Fins.SLDPRT

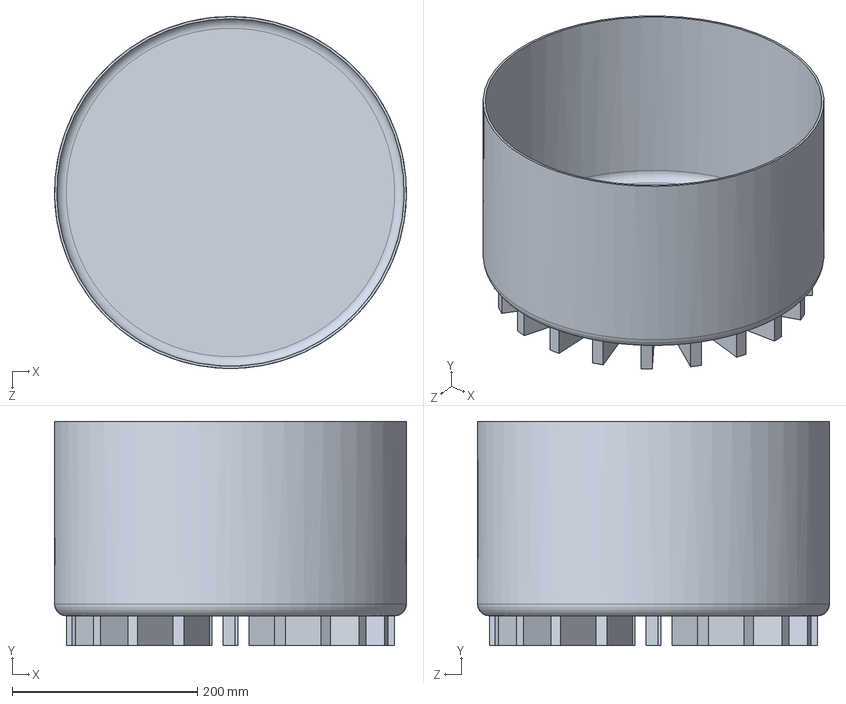
[picture p95: CAD file, 2021-06-08]
Prototypes and Testing--Rice Team/Models _ Simulations/Generation 3 Models - Half Radial Fin Iterations + Fin Guard Models/Life Sized Half Radial Pot_Scaled Fins.SLDPRT
380.0 x 242.3 x 380.0 mm
