PubInv/EcoPot/OpenFOAM/erlenmeyer_pot_16605mm_wall_thickness/constant/geometry/ecoPotContentNew.stl

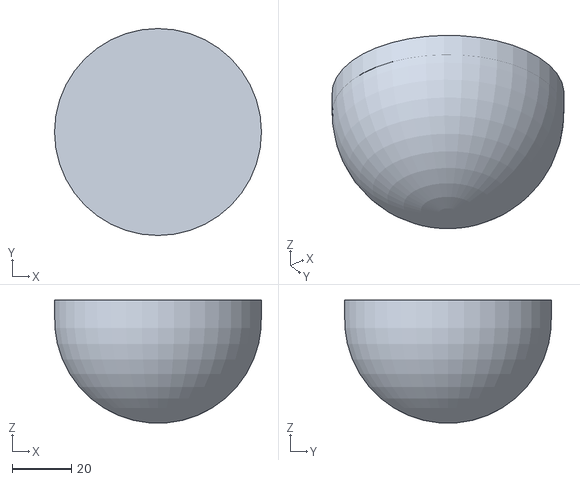
[picture p96: CAD file, 2026-03-23]
OpenFOAM/erlenmeyer_pot_16605mm_wall_thickness/constant/geometry/ecoPotContentNew.stl
70.0 x 70.0 x 41.6
