PubInv/EcoPot/OpenFOAM/optimise_lowResMesh/constant/geometry/robert.stl

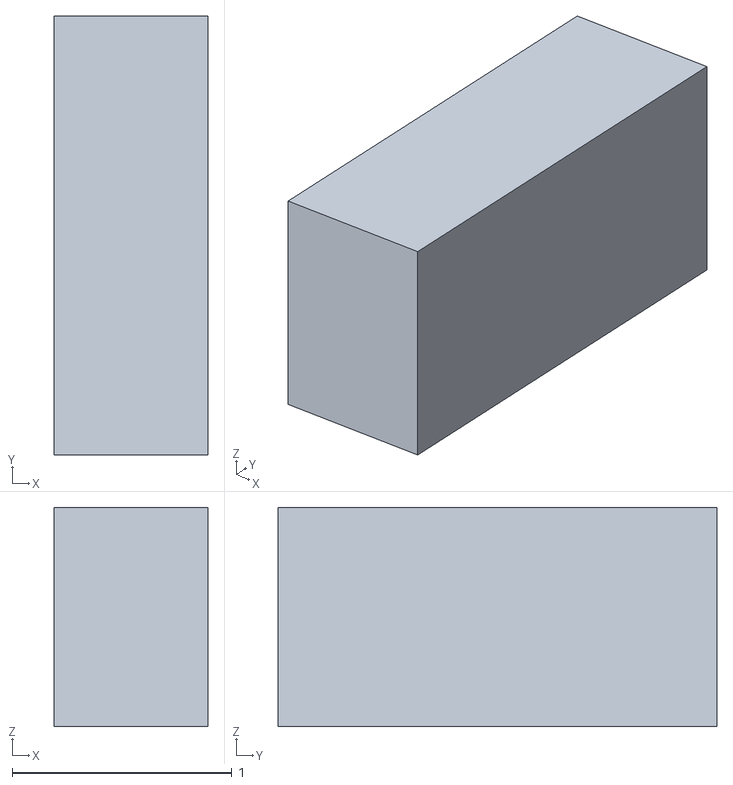
[picture p97: CAD file, 2025-03-31]
OpenFOAM/optimise_lowResMesh/constant/geometry/robert.stl
0.7 x 2.00 x 1.00
