PubInv/EcoPot/pot-designs/Plain_Bottom_Pots.scad

difference () {
cylinder (9,4,4);
translate([0,0,1])cylinder (10,3,3);
}
difference () {
translate ([0,10,4])
sphere(4);
translate ([0,10,6])
sphere(3);
}
difference () {
translate ([0,10,4])
cylinder (5,4,4);
translate ([0,10,5])
cylinder (5,3,3);
    
}
