PubInv/EcoPot/hypo-Round_vs_Flat/Results_RoundPot_Temp_Thick.csv

Time | avg(T)
0.5 | 298.01
1 | 298.04
1.5 | 298.08
2 | 298.12
2.5 | 298.17
3 | 298.23
3.5 | 298.29
4 | 298.36
4.5 | 298.43
5 | 298.51
5.5 | 298.59
6 | 298.67
6.5 | 298.76
7 | 298.85
7.5 | 298.94
8 | 299.04
8.5 | 299.15
9 | 299.26
9.5 | 299.38
10 | 299.5
10.5 | 299.62
11 | 299.75
11.5 | 299.88
12 | 300.01
12.5 | 300.15
13 | 300.3
13.5 | 300.44
14 | 300.59
14.5 | 300.74
15 | 300.9
15.5 | 301.06
16 | 301.22
16.5 | 301.38
17 | 301.55
17.5 | 301.72
18 | 301.89
18.5 | 302.06
19 | 302.23
19.5 | 302.4
20 | 302.57
20.5 | 302.74
21 | 302.92
21.5 | 303.09
22 | 303.27
22.5 | 303.45
23 | 303.62
23.5 | 303.8
24 | 303.99
24.5 | 304.17
25 | 304.35
25.5 | 304.53
26 | 304.72
26.5 | 304.9
27 | 305.09
27.5 | 305.27
28 | 305.46
28.5 | 305.64
29 | 305.83
29.5 | 306.01
30 | 306.19
30.5 | 306.38
31 | 306.57
31.5 | 306.75
32 | 306.94
32.5 | 307.13
33 | 307.31
33.5 | 307.5
34 | 307.69
34.5 | 307.88
35 | 308.07
35.5 | 308.26
36 | 308.45
36.5 | 308.64
37 | 308.83
37.5 | 309.02
38 | 309.21
38.5 | 309.39
39 | 309.58
39.5 | 309.77
40 | 309.95
40.5 | 310.14
41 | 310.32
41.5 | 310.51
42 | 310.69
42.5 | 310.88
43 | 311.06
43.5 | 311.25
44 | 311.43
44.5 | 311.62
45 | 311.8
45.5 | 311.99
46 | 312.18
46.5 | 312.37
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
