PubInv/EcoPot/Prototypes and Testing--Rice Team/Comparative Test Between Current Market Pots/Edits/GSI small.gif

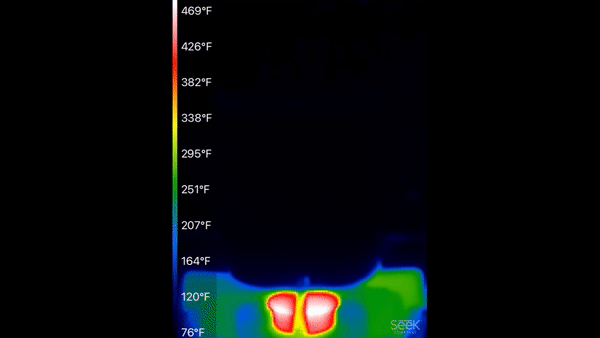
Prototypes and Testing--Rice Team/Comparative Test Between Current Market Pots/Edits/GSI small.gif
