PubInv/EcoPot/Prototypes and Testing--Rice Team/IR Camera/First OEDk/IMG_0001.jpg

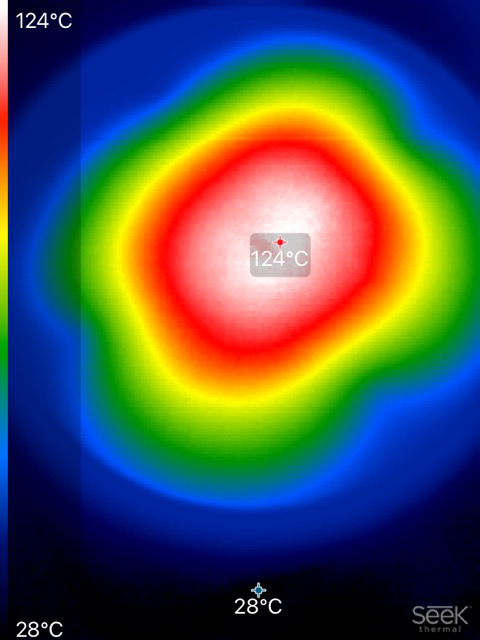
Prototypes and Testing--Rice Team/IR Camera/First OEDk/IMG_0001.jpg
