PubInv/EcoPot/Prototypes and Testing--Rice Team/IR Camera/First OEDk/IMG_0002.jpg

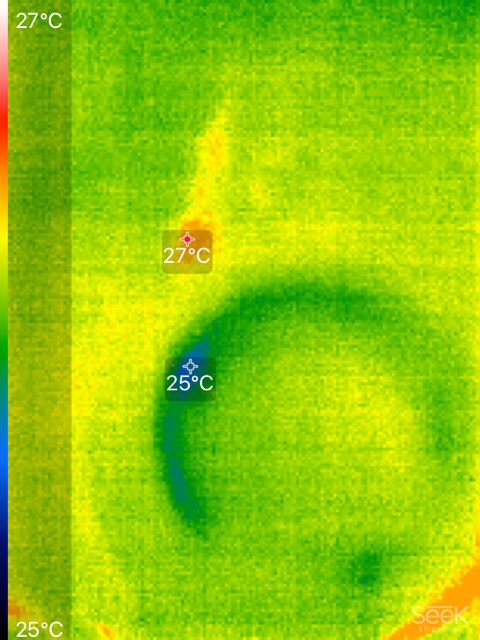
Prototypes and Testing--Rice Team/IR Camera/First OEDk/IMG_0002.jpg
