PubInv/EcoPot/Prototypes and Testing--Rice Team/IR Camera/First OEDk/IMG_0003.jpg

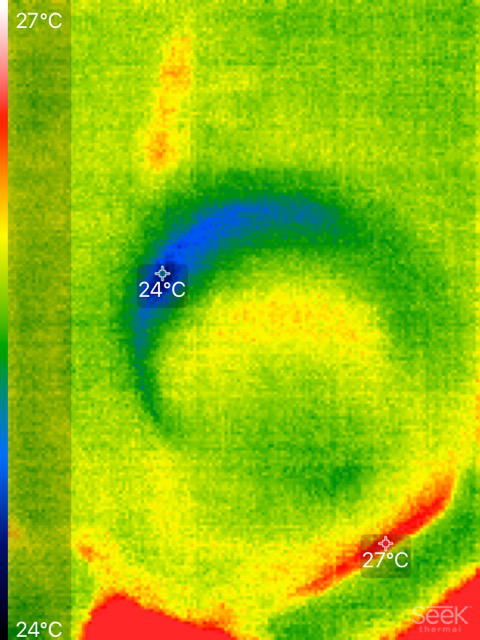
Prototypes and Testing--Rice Team/IR Camera/First OEDk/IMG_0003.jpg
