PubInv/EcoPot/Prototypes and Testing--Rice Team/IR Camera/First OEDk/IMG_0004.jpg

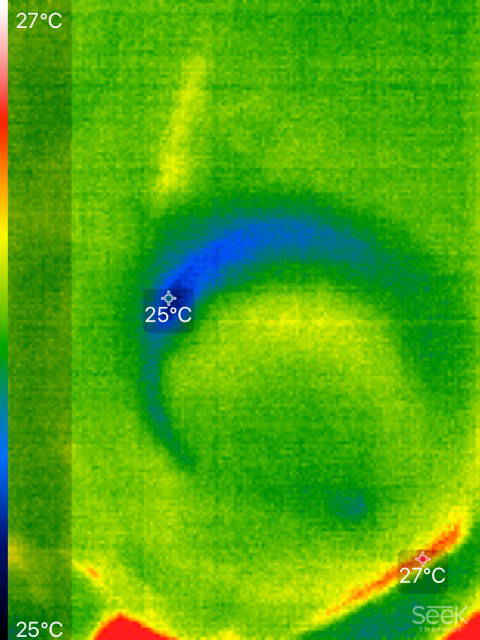
Prototypes and Testing--Rice Team/IR Camera/First OEDk/IMG_0004.jpg
