PubInv/EcoPot/Prototypes and Testing--Rice Team/IR Camera/First OEDk/IMG_3756.JPG

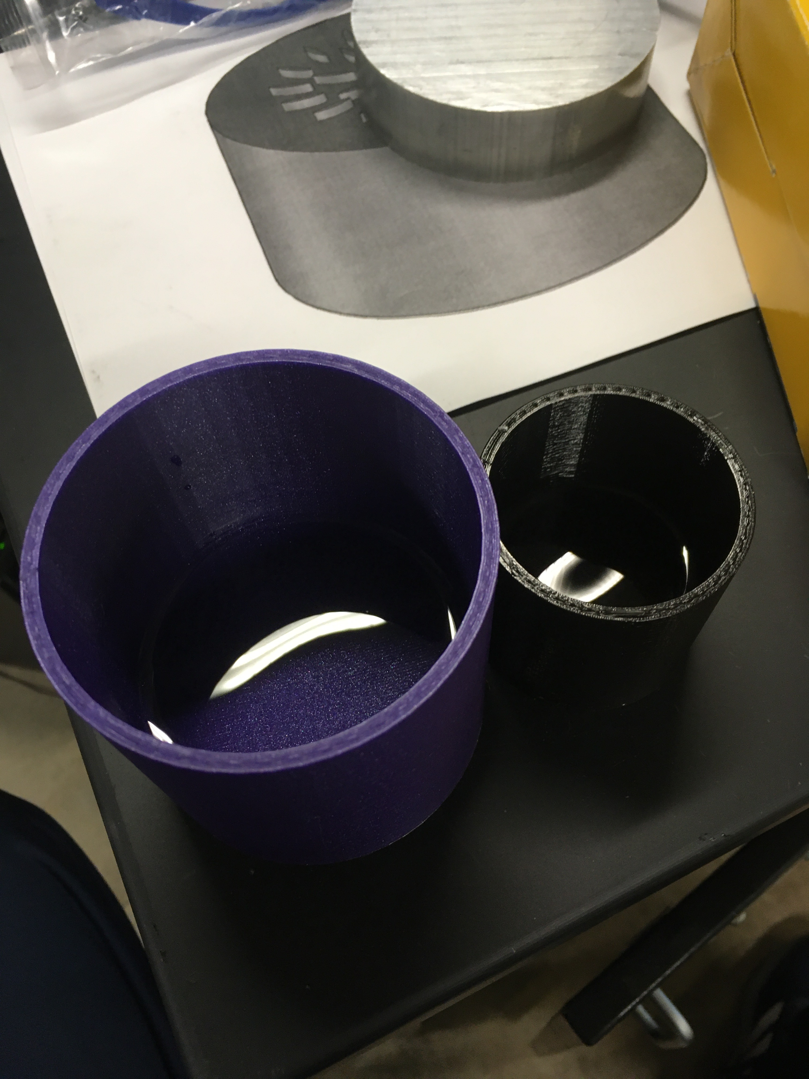
Prototypes and Testing--Rice Team/IR Camera/First OEDk/IMG_3756.JPG
