PubInv/EcoPot/Prototypes and Testing--Rice Team/IR Camera/First test (Open Flame)/IMG_0003(1).jpg

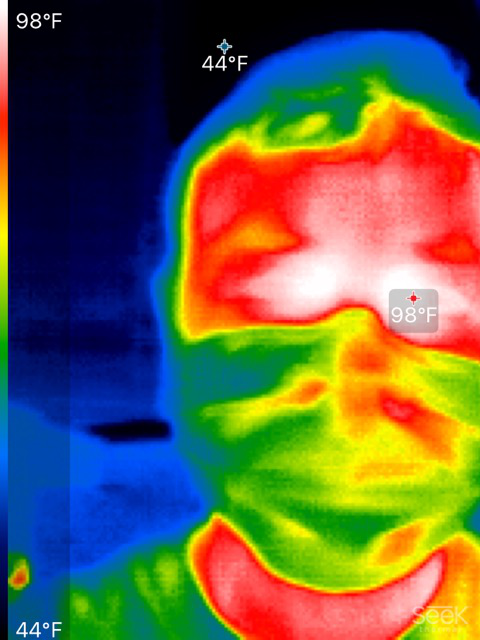
Prototypes and Testing--Rice Team/IR Camera/First test (Open Flame)/IMG_0003(1).jpg
