PubInv/EcoPot/Prototypes and Testing--Rice Team/IR Camera/First test (Open Flame)/IMG_0004.jpg

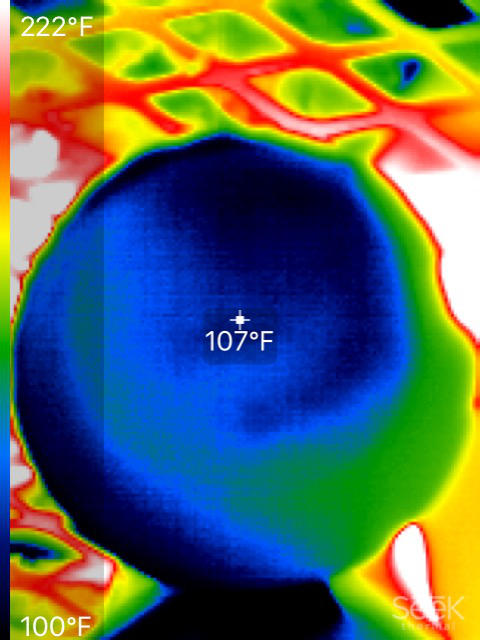
Prototypes and Testing--Rice Team/IR Camera/First test (Open Flame)/IMG_0004.jpg
