PubInv/EcoPot/Prototypes and Testing--Rice Team/IR Camera/First test (Open Flame)/IMG_0006.jpg

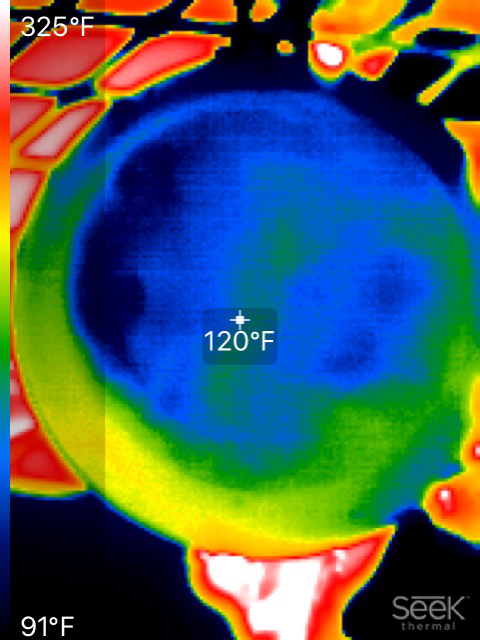
Prototypes and Testing--Rice Team/IR Camera/First test (Open Flame)/IMG_0006.jpg
