PubInv/EcoPot/issues/turbulence-inside-pot/Screenshot 2025-11-10 171323.png

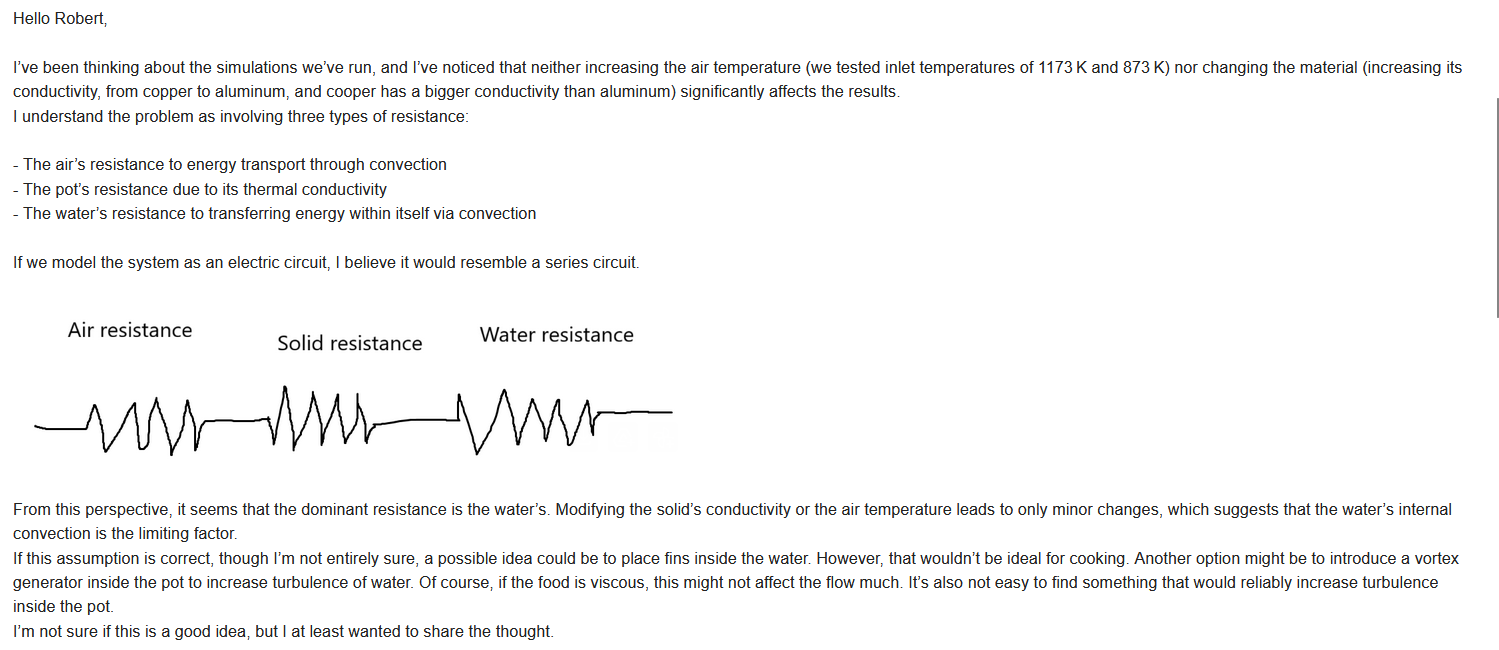
issues/turbulence-inside-pot/Screenshot 2025-11-10 171323.png
