PubInv/EcoPot/Prototypes and Testing--Rice Team/IR Camera/First test (Open Flame)/IMG_3673.JPG

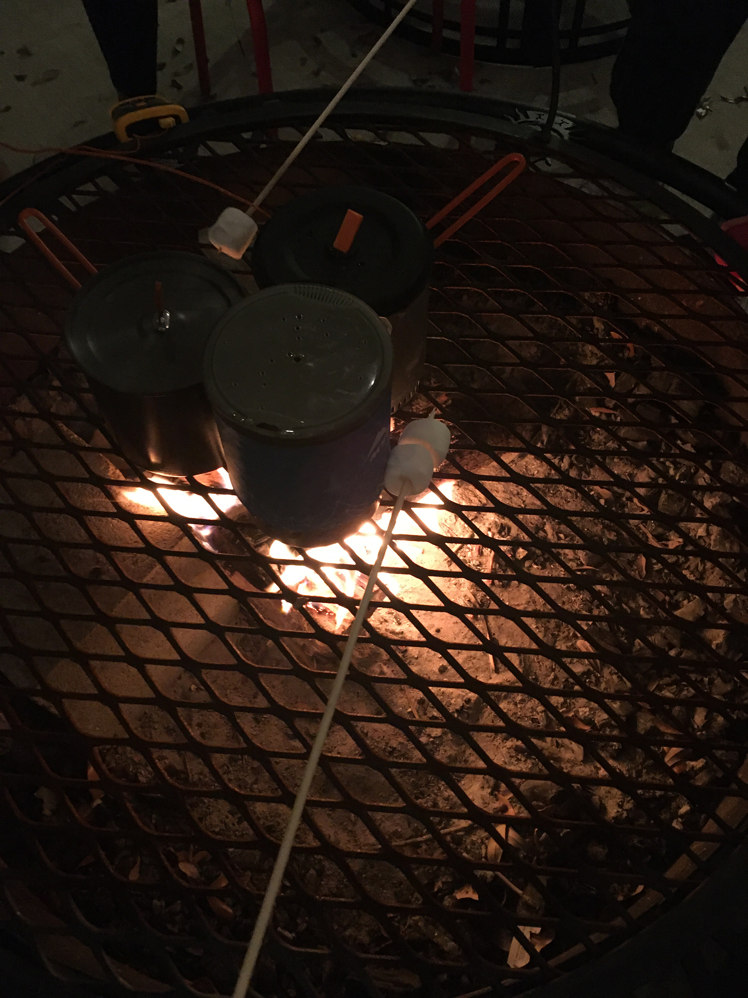
Prototypes and Testing--Rice Team/IR Camera/First test (Open Flame)/IMG_3673.JPG
